mustafab0/Bionic-Arm/Design/Final/mini-dc-geared-motor-1.snapshot.2/mini dc geared motor02.JPG

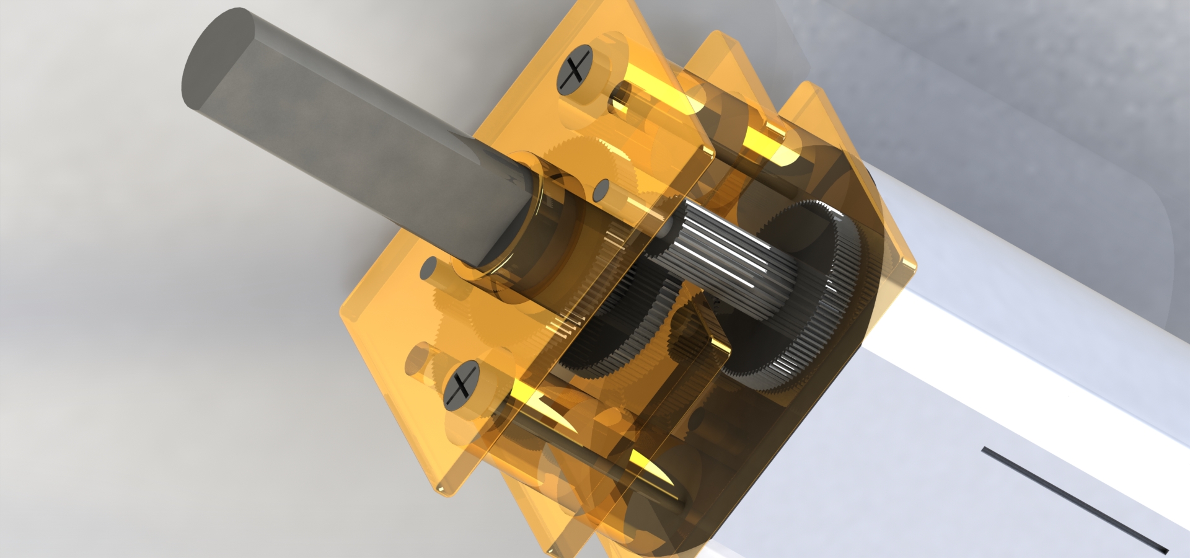
Design/Final/mini-dc-geared-motor-1.snapshot.2/mini dc geared motor02.JPG
