mustafab0/Bionic-Arm/Design/Final/mini-dc-geared-motor-1.snapshot.2/mini dc geared motor03.JPG

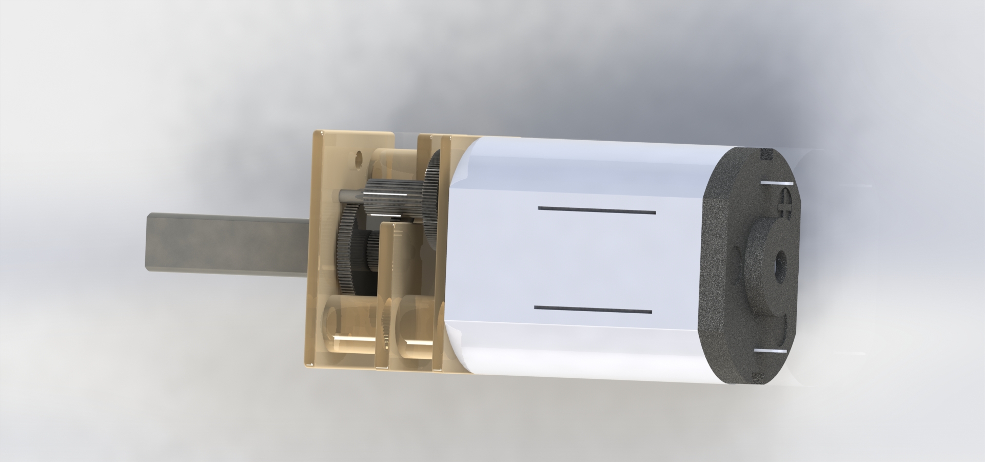
Design/Final/mini-dc-geared-motor-1.snapshot.2/mini dc geared motor03.JPG
