mustafab0/Bionic-Arm/Design/Final/mini-dc-geared-motor-1.snapshot.2/motorDC01.jpg

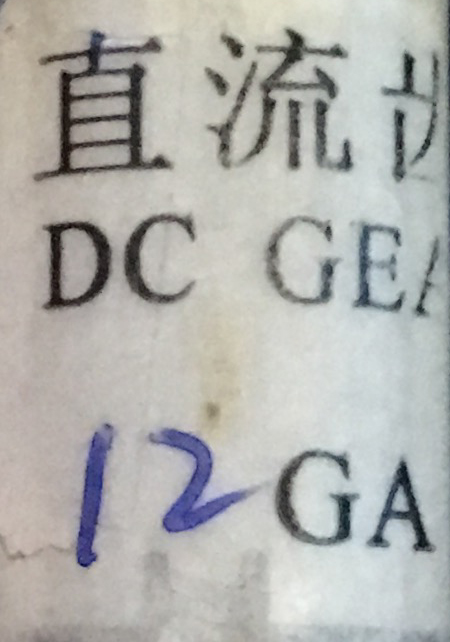
Design/Final/mini-dc-geared-motor-1.snapshot.2/motorDC01.jpg
