mustafab0/Bionic-Arm/Design/Final/mini-dc-geared-motor-1.snapshot.2/motorDC02.jpg

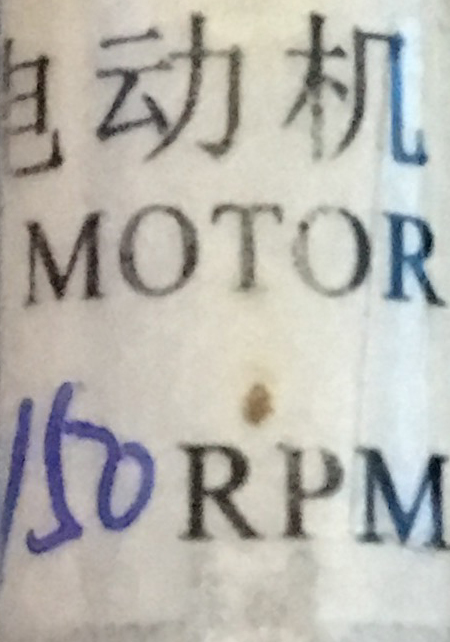
Design/Final/mini-dc-geared-motor-1.snapshot.2/motorDC02.jpg
