mustafab0/Bionic-Arm/Design/Hand/546.JPG

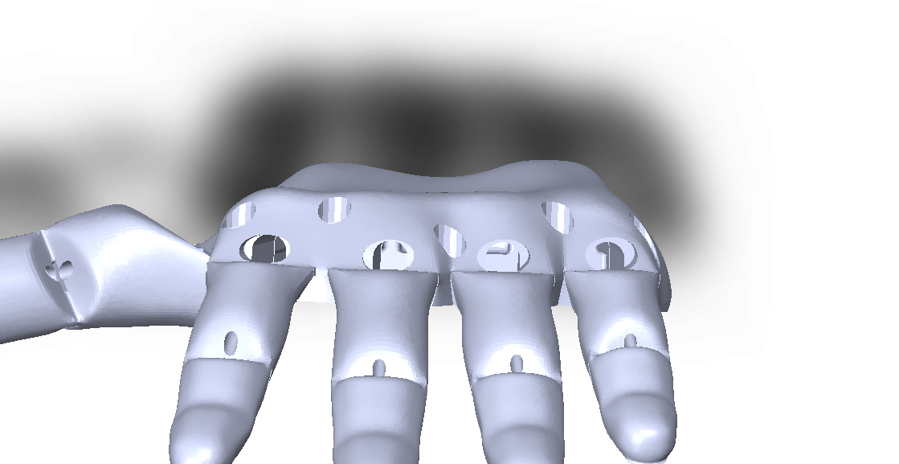
Design/Hand/546.JPG
