mustafab0/Bionic-Arm/Design/Hand/Arm.PNG

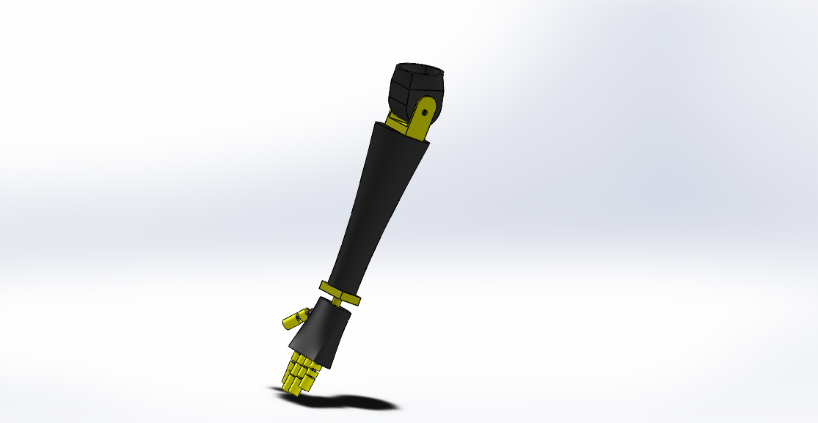
Design/Hand/Arm.PNG
