mustafab0/Bionic-Arm/Design/Images/Palm2.1.JPG

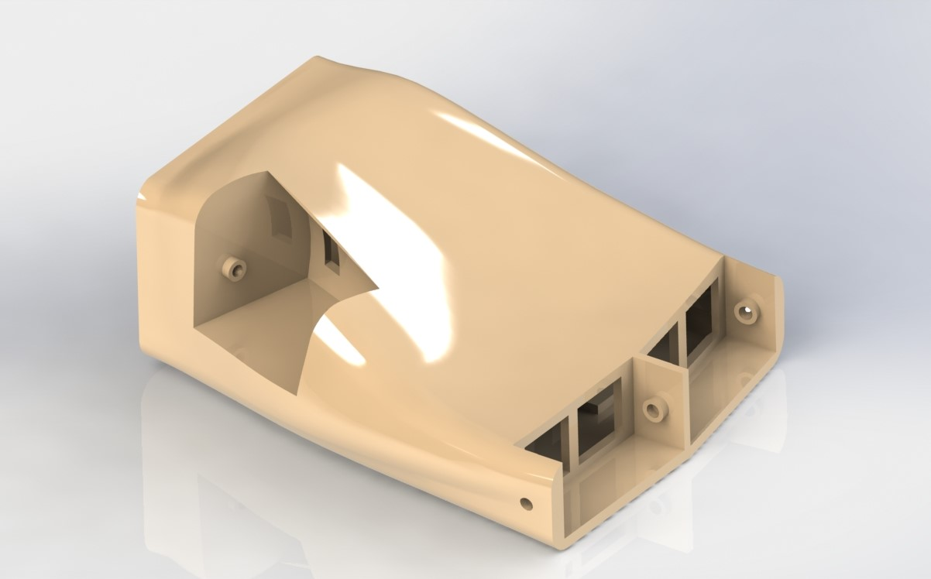
Design/Images/Palm2.1.JPG
