mustafab0/Bionic-Arm/Design/Palm/1.x/IMG_20170302_203847119.jpg

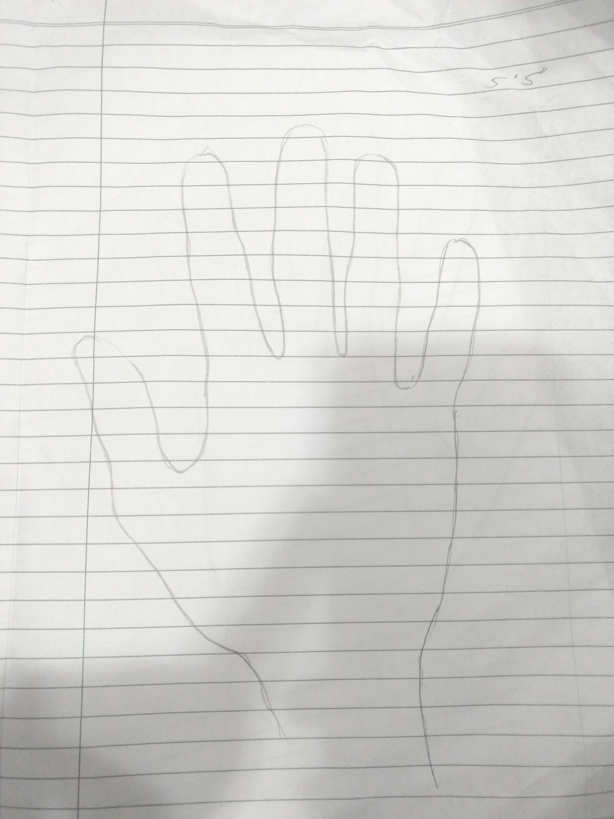
Design/Palm/1.x/IMG_20170302_203847119.jpg
