mustafab0/Bionic-Arm/Design/Fingers/2ndDigit/1.x/Index1.1.SLDASM

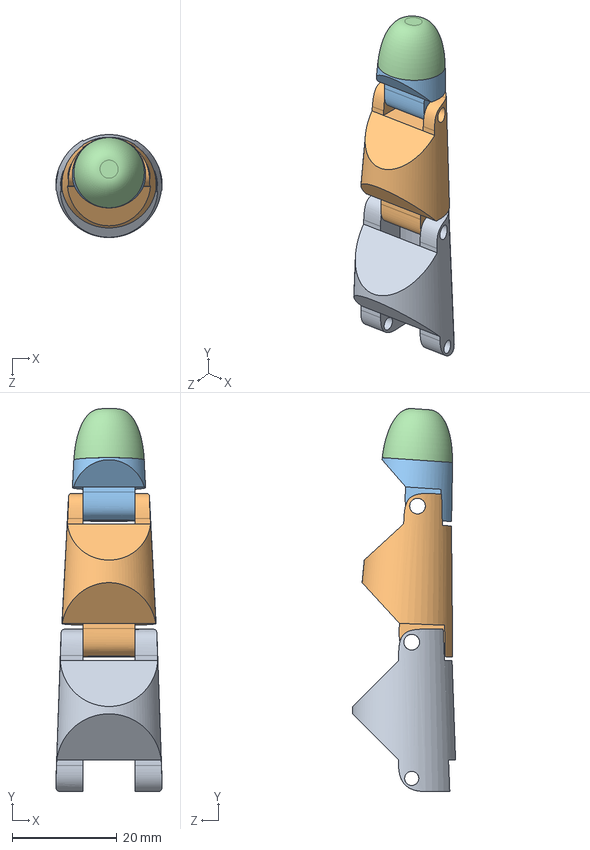
[picture p99: CAD file, 2022-01-19]
Design/Fingers/2ndDigit/1.x/Index1.1.SLDASM
20.3 x 73.1 x 19.7 mm
IBase1.1
IMid1.1
ITop1.1
ICap
