mustafab0/Bionic-Arm/Design/Fingers/3rdDigit/1.x/Middle1.1.1.SLDASM

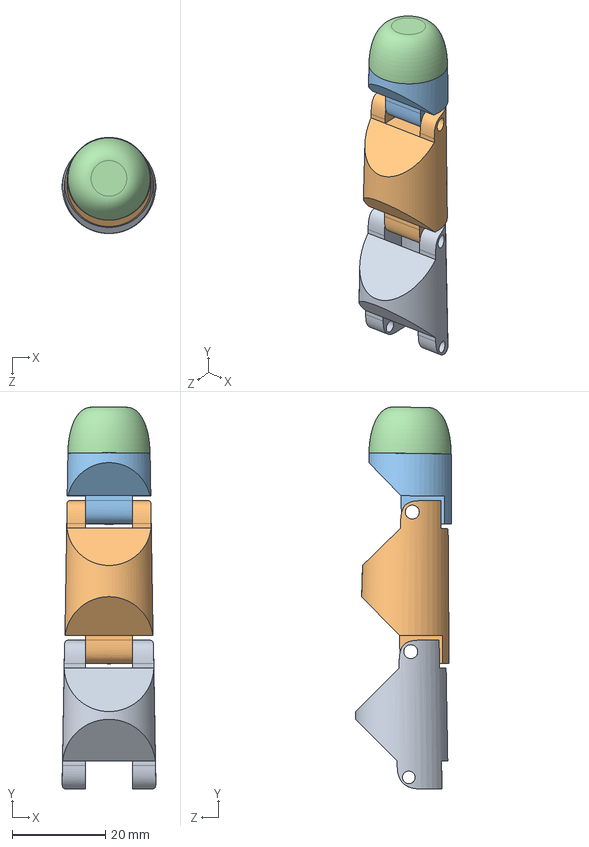
[picture p100: CAD file, 2022-01-19]
Design/Fingers/3rdDigit/1.x/Middle1.1.1.SLDASM
20.2 x 82.1 x 20.7 mm
MBase1.1
MMid1.1.1
MTop1.1.1
MCap1.1.1
