mustafab0/Bionic-Arm/Design/Hand/Assem2.0.1.SLDASM

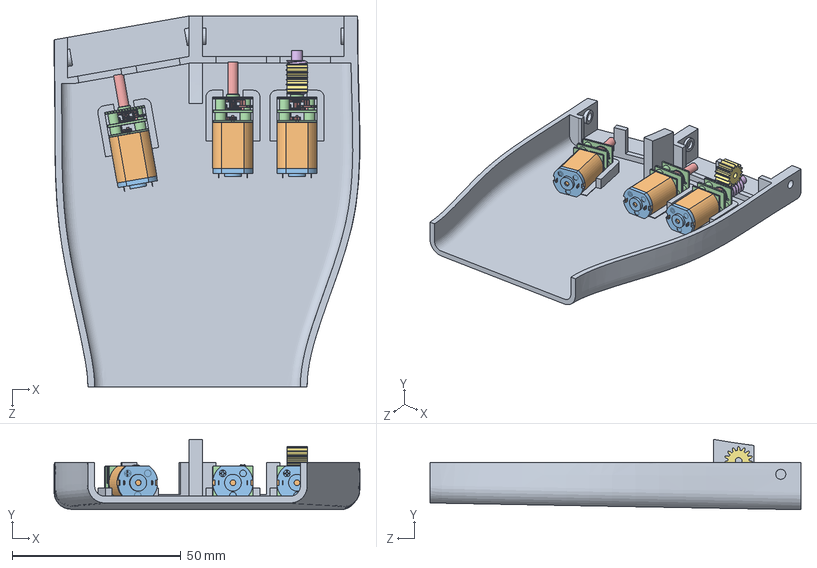
[picture p101: CAD file, 2022-01-19]
Design/Hand/Assem2.0.1.SLDASM
90.7 x 20.9 x 110.0 mm
Palm2.0.1
DC_GE_RED_Motor_01 x 3
DC_GE_RED_Motor_02 x 3
DC_GE_RED_Motor_03 x 3
DC_GE_RED_Motor_04 x 3
Worm Gear
spur gear_am
