mustafab0/Bionic-Arm/Design/Hand/BE Project/Assem3.1.1.SLDASM

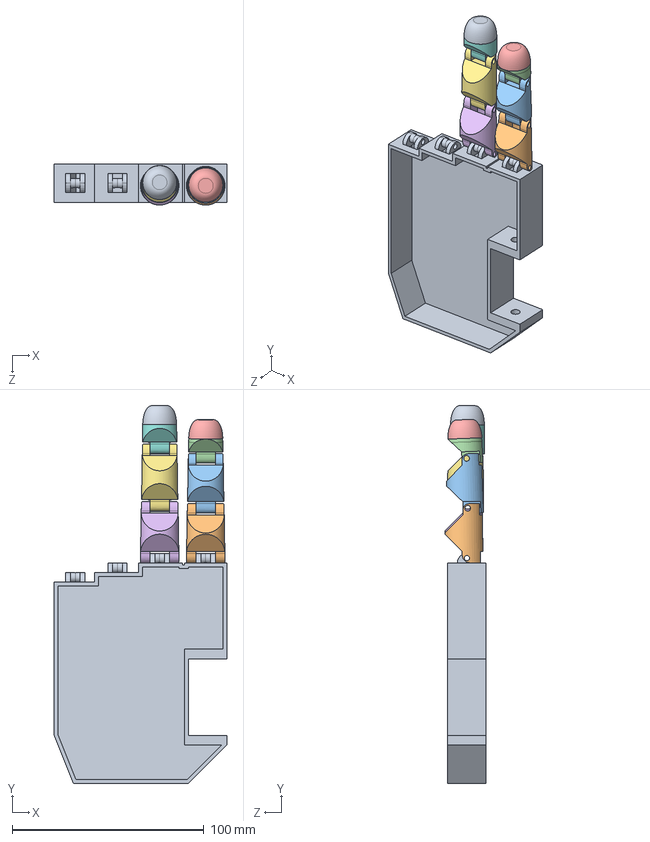
[picture p102: CAD file, 2022-01-19]
Design/Hand/BE Project/Assem3.1.1.SLDASM
90.0 x 197.1 x 21.5 mm
Palm1.0.1
IBase1.3
IMid1.3.1
ITop1.3.1
ICap1.3.1
MBase1.1
MMid1.1.1
MTop1.1.1
MCap1.1.1
