mustafab0/Bionic-Arm/Design/Fingers/1stDigit/1.x/Thumb1.0.SLDASM

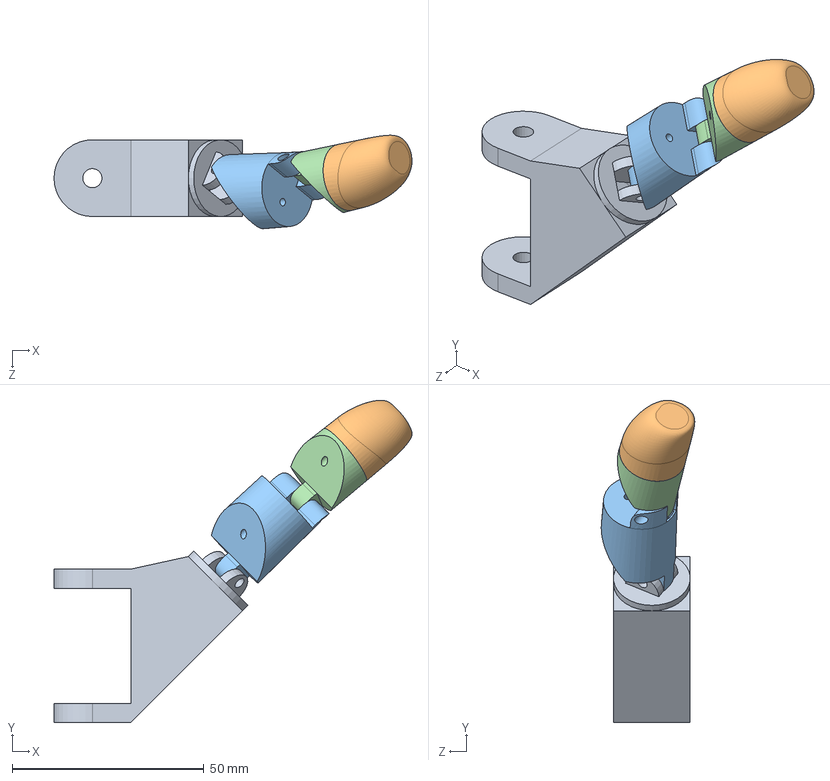
[picture p103: CAD file, 2022-01-19]
Design/Fingers/1stDigit/1.x/Thumb1.0.SLDASM
93.3 x 84.0 x 24.4 mm
TBase1.0
TCap1.0
TMid1.0
TTop1.0
