mustafab0/Bionic-Arm/Design/Fingers/3rdDigit/1.x/Middle1.0.SLDASM

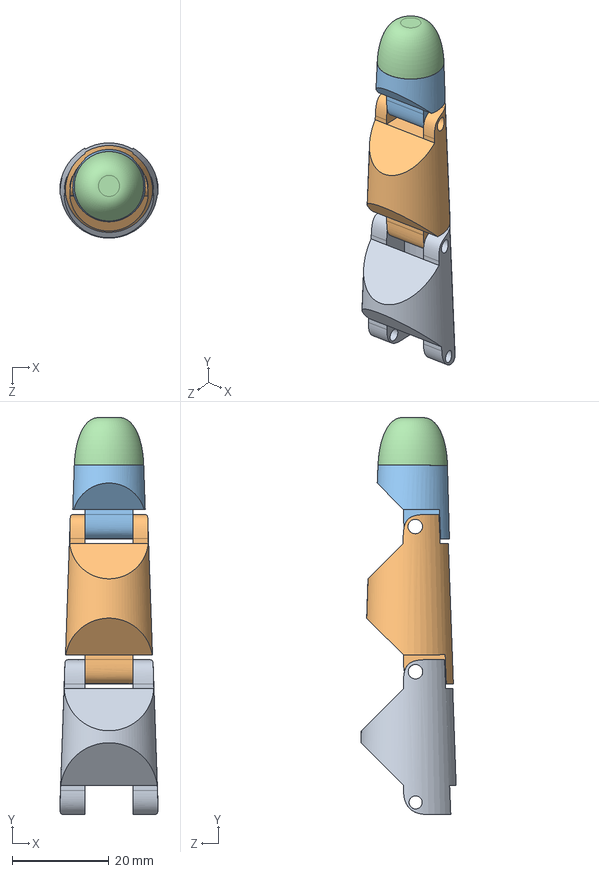
[picture p104: CAD file, 2022-01-19]
Design/Fingers/3rdDigit/1.x/Middle1.0.SLDASM
20.3 x 82.0 x 19.7 mm
MBase1.0
MMid1.0
MTop1.0
MCap1.0
