mustafab0/Bionic-Arm/Design/Palm/2.x/2.0.x/Assem2.SLDASM

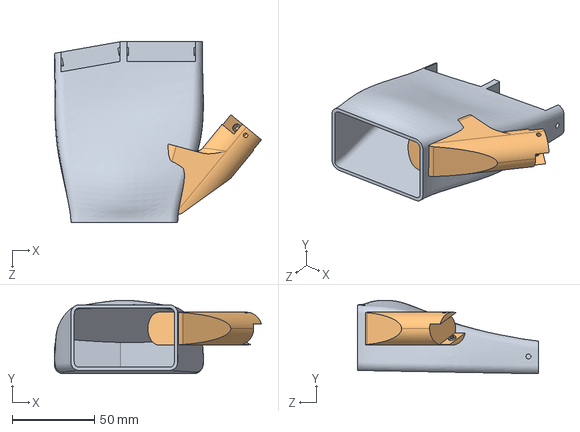
[picture p106: CAD file, 2022-01-19]
Design/Palm/2.x/2.0.x/Assem2.SLDASM
126.1 x 44.8 x 110.0 mm
Palm2.0
tProximal2.0
