mustafab0/Bionic-Arm/Design/Fingers/1stDigit/2.x/1Digit2.3.SLDASM

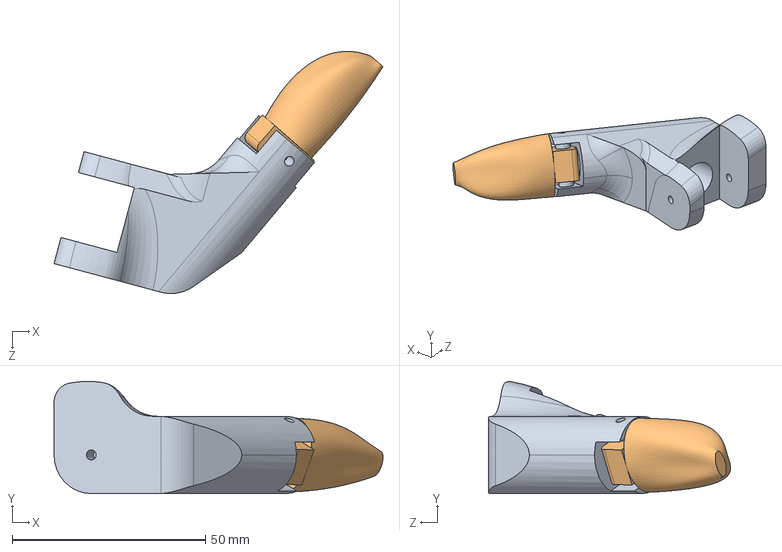
[picture p107: CAD file, 2022-01-19]
Design/Fingers/1stDigit/2.x/1Digit2.3.SLDASM
85.2 x 29.0 x 62.7 mm
tProximal2.3
tDistal2.0
