mustafab0/Bionic-Arm/Design/Hand/YadEKalKhair2.0Alternative mechanism.SLDASM

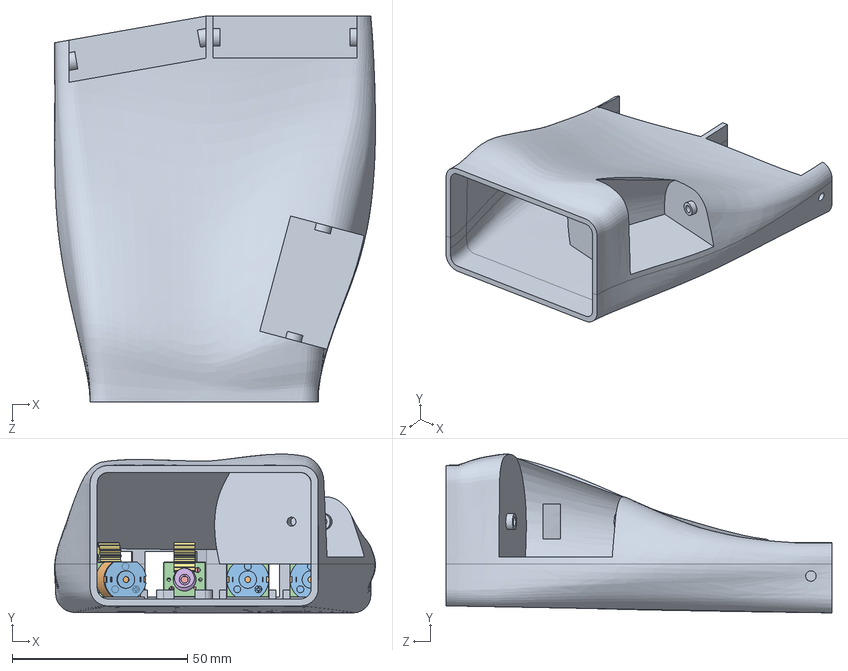
[picture p109: CAD file, 2022-01-19]
Design/Hand/YadEKalKhair2.0Alternative mechanism.SLDASM
91.5 x 45.3 x 110.0 mm
Palm2.2
DC_GE_RED_Motor_01 x 4
DC_GE_RED_Motor_02 x 4
DC_GE_RED_Motor_03 x 4
DC_GE_RED_Motor_04 x 4
Worm x 4
Spur Gear x 4
