mustafab0/Bionic-Arm/Design/Fingers/2ndDigit/1.x/Index1.2.SLDASM

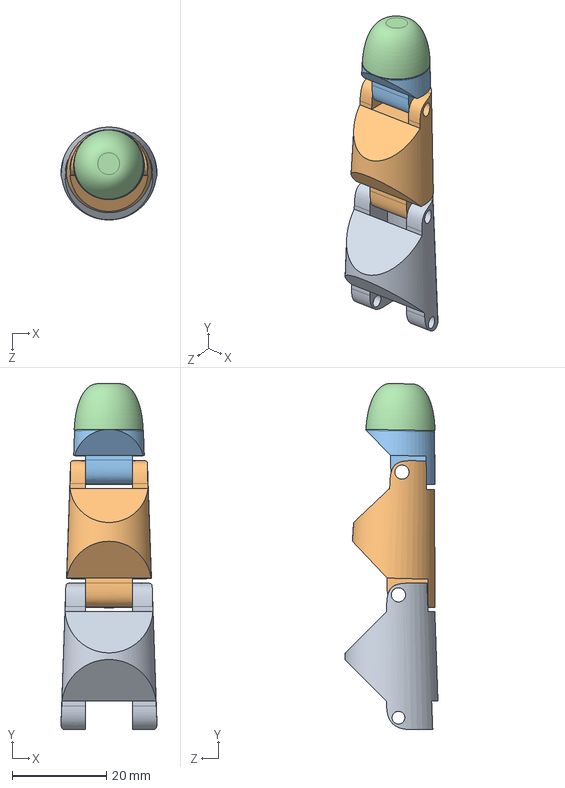
[picture p110: CAD file, 2022-01-19]
Design/Fingers/2ndDigit/1.x/Index1.2.SLDASM
20.3 x 73.3 x 19.7 mm
IBase1.1
IMid1.2
ITop1.2
ICap1.2
