mustafab0/Bionic-Arm/Design/Hand/BE Project/Assem1.SLDASM

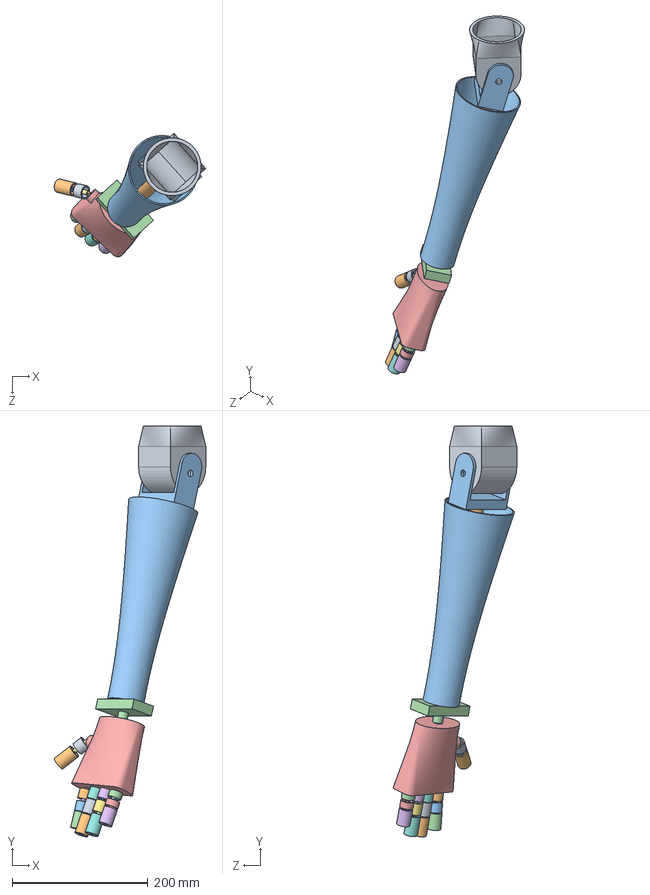
[picture p111: CAD file, 2022-01-19]
Design/Hand/BE Project/Assem1.SLDASM
223.2 x 605.1 x 182.0 mm
Stump1.0
ArmShaft1.0
Brace1.0
Brce
Palm1
IndexLFramework
IndexMFramework
IndexUFramework
Framework pin x 9
IndexL
IndexM
IndexU
MiddleLFramework
MiddleMFramework
MiddleUFramework
MiddleL
MiddleM
MiddleU
RingLFramework
RingMFramework
RingUFramework
RingL
RingM
RingU
PinkyLFramework
PinkyMFramework
PinkyUFramework
PinkyL
PinkyM
PinkyU
ThumbLFramework
ThumbUFramework
ThumbL
ThumbU
ArmCover
