mustafab0/Bionic-Arm/Design/Fingers/1stDigit/1.x/Thumb1.1.SLDASM

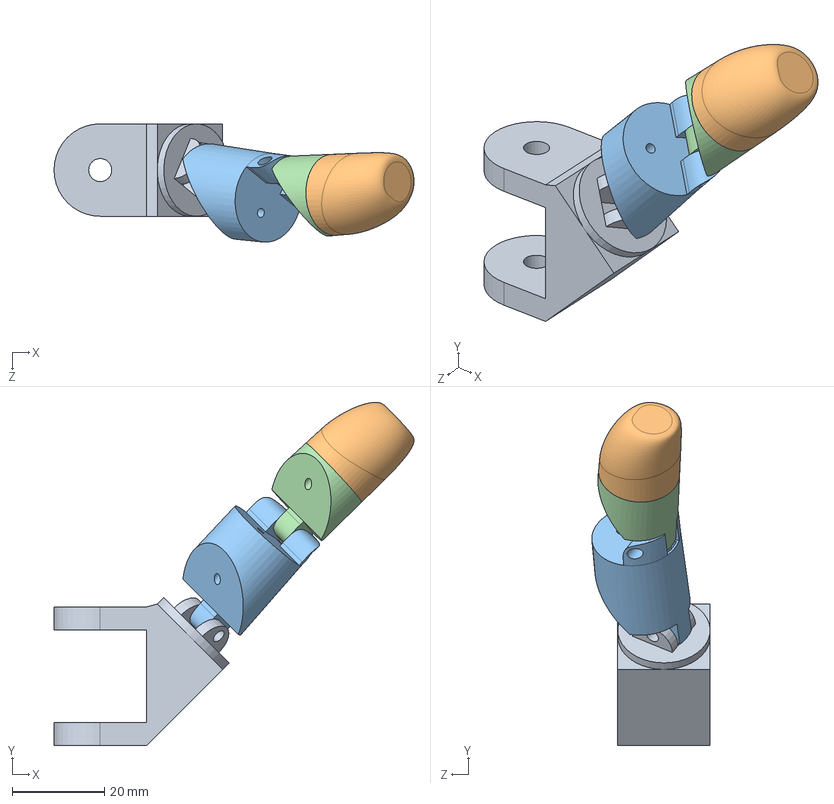
[picture p112: CAD file, 2022-01-19]
Design/Fingers/1stDigit/1.x/Thumb1.1.SLDASM
77.9 x 74.3 x 25.6 mm
TBase1.1
TCap1.0
TMid1.0
TTop1.0
