mustafab0/Bionic-Arm/Design/Fingers/1stDigit/2.x/1Digit2.2.SLDASM

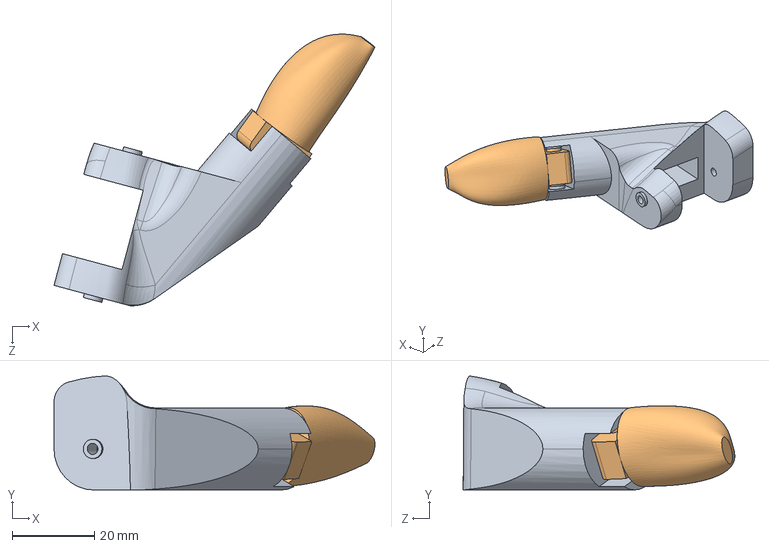
[picture p113: CAD file, 2022-01-19]
Design/Fingers/1stDigit/2.x/1Digit2.2.SLDASM
78.2 x 27.7 x 66.2 mm
tProximal2.2
tDistal2.0
