mustafab0/Bionic-Arm/Design/Fingers/3rdDigit/2.x/2.0/3Digit2.0.SLDASM

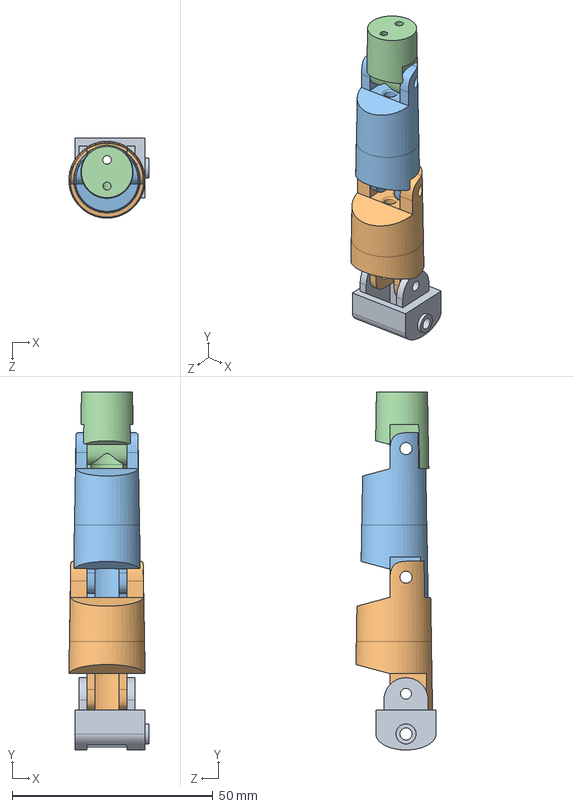
[picture p114: CAD file, 2022-01-19]
Design/Fingers/3rdDigit/2.x/2.0/3Digit2.0.SLDASM
20.0 x 89.1 x 20.0 mm
mMetaCarpal2.0
mProximal2.0
mIntermediate2.0
mDistal2.0
