mustafab0/Bionic-Arm/Design/Hand/BE Project/Assem.SLDASM

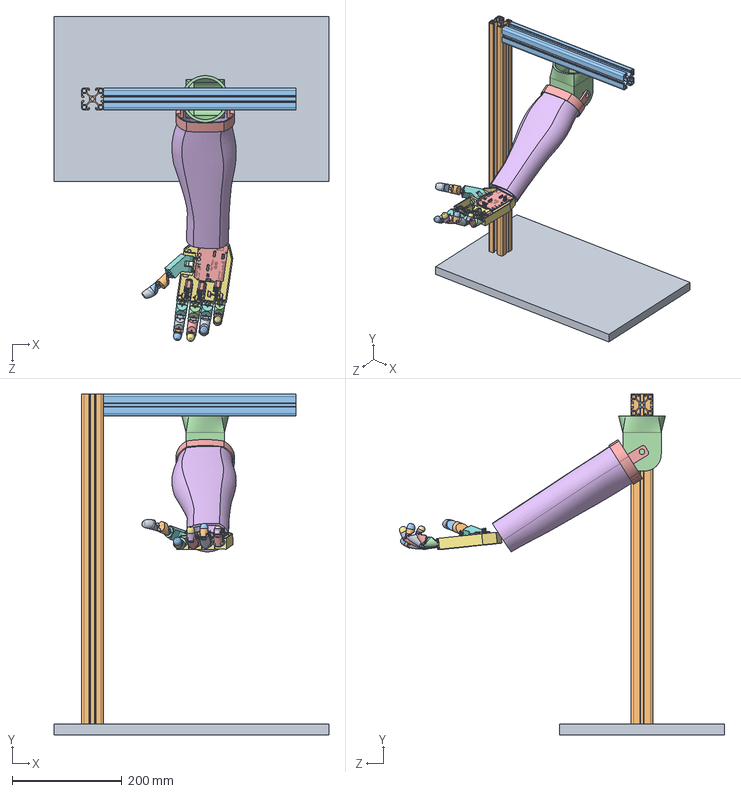
[picture p115: CAD file, 2022-01-19]
Design/Hand/BE Project/Assem.SLDASM
500.0 x 620.0 x 590.9 mm
Stump1.1
Brace1.1
ArmCover1.2
Palm1.0.4
IBase1.3
IMid1.3
ITop1.3
ICap1.3
Pulley Gear Shaft x 4
DC_GE_RED_Motor_01 x 4
DC_GE_RED_Motor_02 x 4
DC_GE_RED_Motor_03 x 4
DC_GE_RED_Motor_04 x 4
Worm Gear x 4
Pulley x 5
spur gear_am x 4
MBase1.1
MMid1.1
MTop1.1
MCap1.1
RBase1.0
RMid1.0
RTop1.0
RCap1.0
PBase1.0
PMid1.1
PTop1.1
PCap1.1
TBase1.2
TCap1.0
TMid1.0
TTop1.0
Pin
Arduino board
