mustafab0/Bionic-Arm/Design/Fingers/4thDigit/2.x/2.0/4Digit2.0.SLDASM

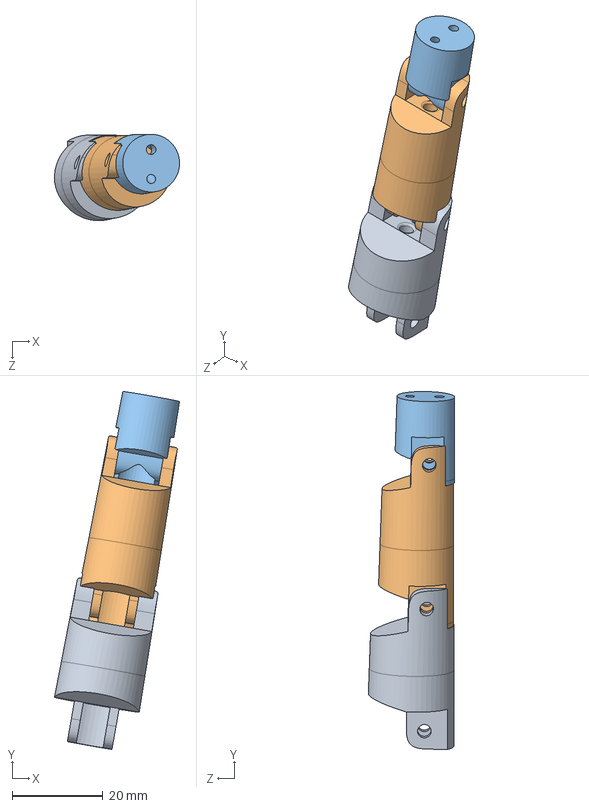
[picture p116: CAD file, 2022-01-19]
Design/Fingers/4thDigit/2.x/2.0/4Digit2.0.SLDASM
27.6 x 79.0 x 19.0 mm
rProximal2.0
rIntermediate2.0
rDistal2.0
