mustafab0/Bionic-Arm/Design/Fingers/5thDigit/1.x/Pinky1.0.SLDASM

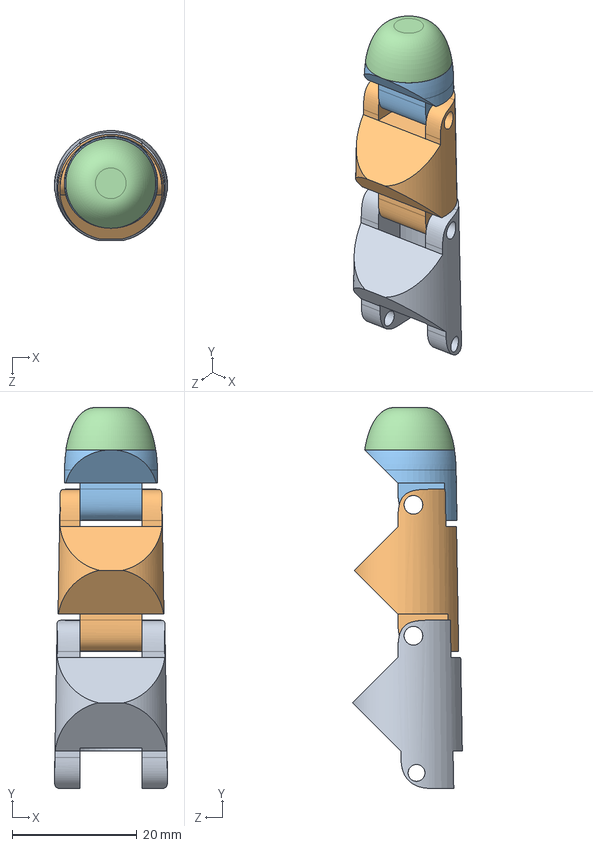
[picture p117: CAD file, 2022-01-19]
Design/Fingers/5thDigit/1.x/Pinky1.0.SLDASM
18.2 x 61.1 x 17.6 mm
PBase1.0
PMid1.0
PTop1.0
PCap1.0
