mustafab0/Bionic-Arm/Design/Fingers/5thDigit/2.x/5Digit2.0.SLDASM

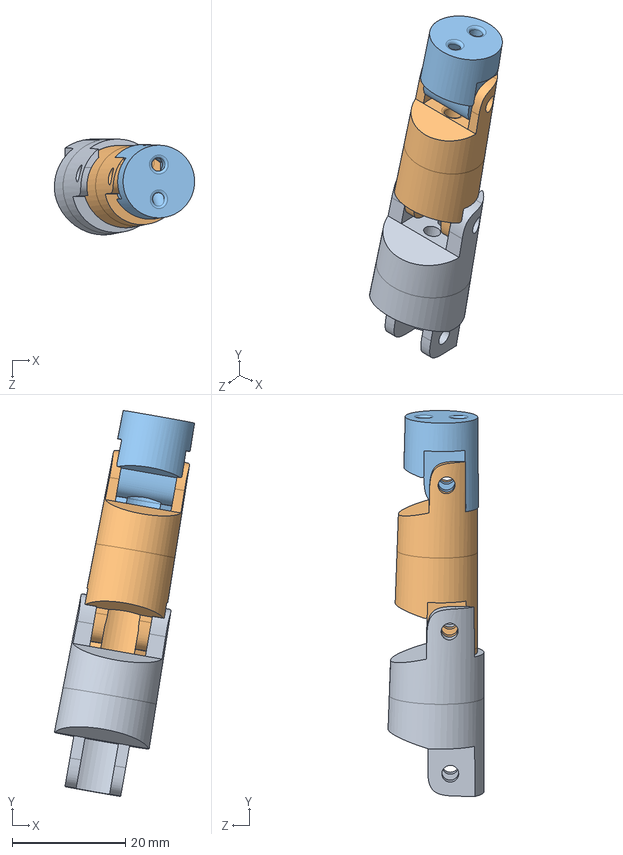
[picture p118: CAD file, 2022-01-19]
Design/Fingers/5thDigit/2.x/5Digit2.0.SLDASM
24.8 x 68.2 x 16.9 mm
pProximal2.0
pIntermediate2.0
pDistal2.0
