mustafab0/Bionic-Arm/Design/Fingers/1stDigit/1.x/Thumb1.2.SLDASM

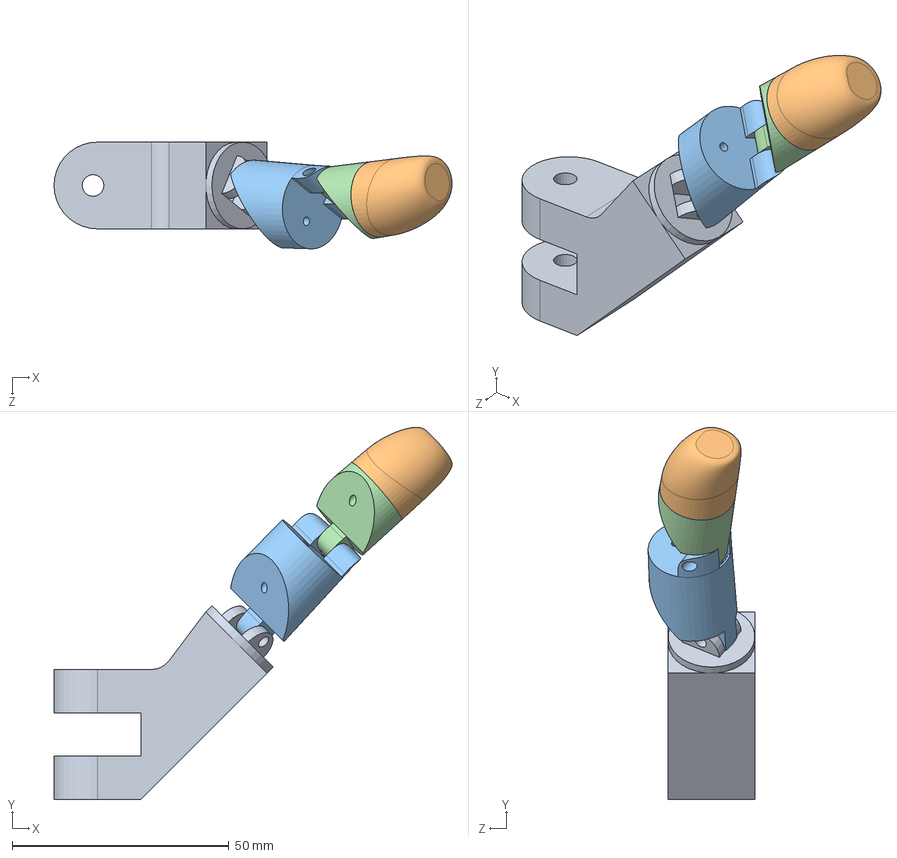
[picture p119: CAD file, 2022-01-19]
Design/Fingers/1stDigit/1.x/Thumb1.2.SLDASM
91.8 x 85.8 x 24.6 mm
TBase1.2
TCap1.0
TMid1.0
TTop1.0
