mustafab0/Bionic-Arm/Design/Hand/BE Project/Assem4.SLDASM

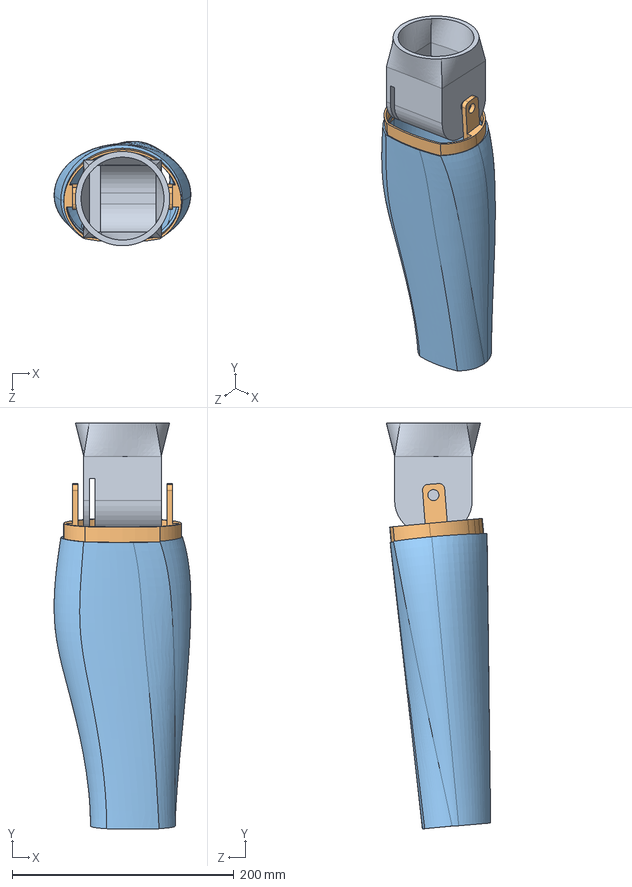
[picture p120: CAD file, 2022-01-19]
Design/Hand/BE Project/Assem4.SLDASM
123.3 x 366.0 x 94.2 mm
Stump1.1
Brace1.1
ArmCover1.1
