mustafab0/Bionic-Arm/Design/Hand/BE Project/Assem5.SLDASM

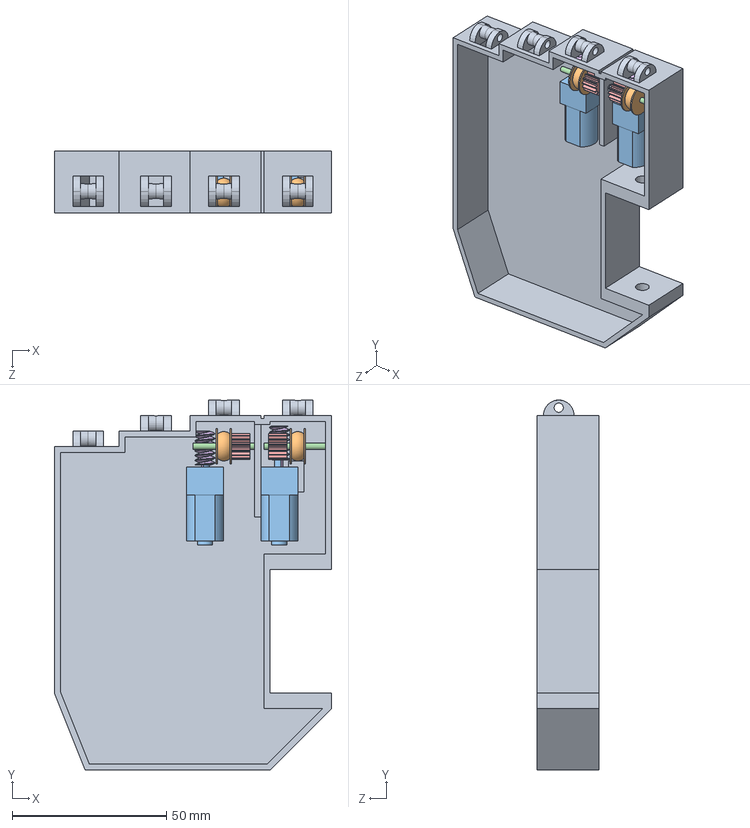
[picture p121: CAD file, 2022-01-19]
Design/Hand/BE Project/Assem5.SLDASM
90.0 x 120.0 x 20.0 mm
Palm1.0.2
Small Pulley x 2
Mini DC Motor x 2
Pulley Gear Shaft x 2
spur gear_am x 2
Worm Gear x 2
