mustafab0/Bionic-Arm/Design/Final/Assem1.SLDASM

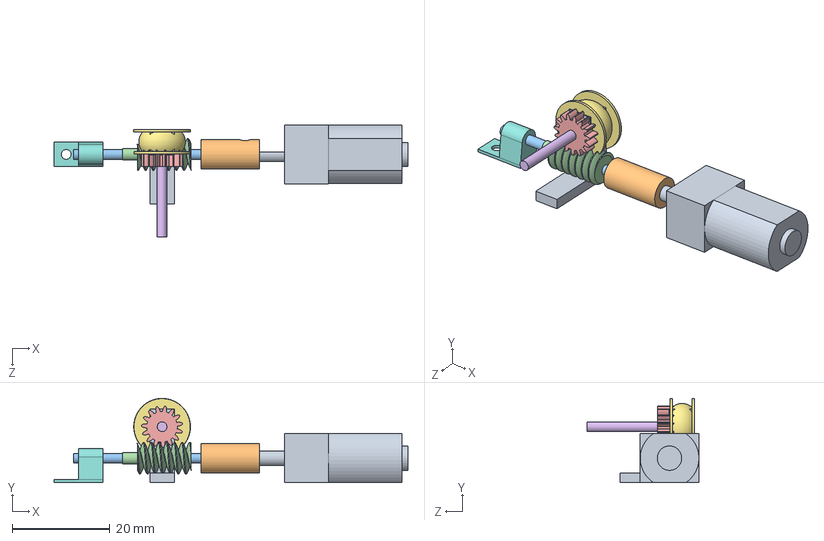
[picture p122: CAD file, 2022-01-19]
Design/Final/Assem1.SLDASM
72.3 x 17.2 x 22.9 mm
Mini DC Motor
Coupling
Shaft for coupling n
Worm Gear
spur gear_am
Pulley Gear Shaft
Small Pulley
Support
Support1
