mustafab0/Bionic-Arm/Design/Fingers/3rdDigit/1.x/Middle1.1.SLDASM

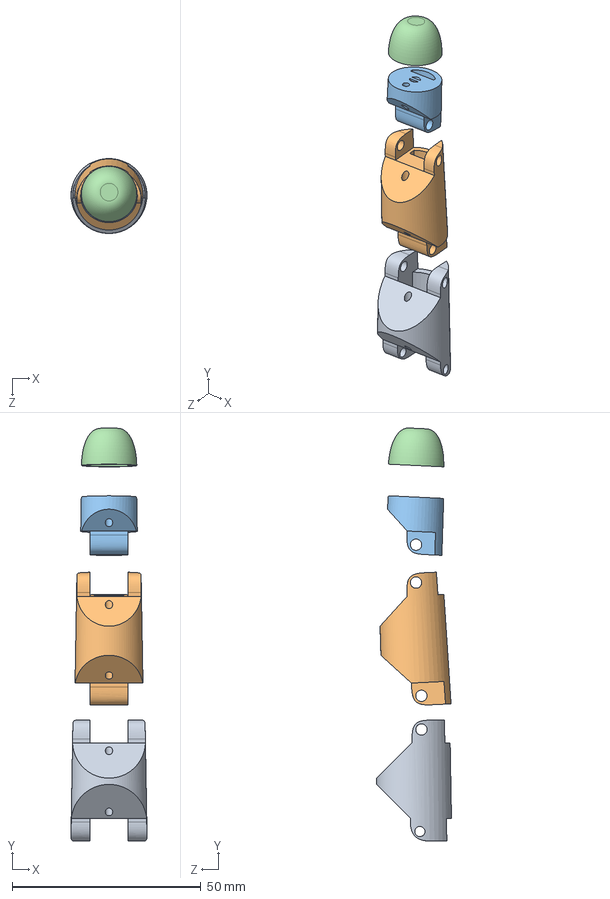
[picture p123: CAD file, 2022-01-19]
Design/Fingers/3rdDigit/1.x/Middle1.1.SLDASM
20.2 x 109.3 x 19.8 mm
MBase1.1
MMid1.1
MTop1.1
MCap1.1
