mustafab0/Bionic-Arm/Design/Hand/BE Project/Assem3.1.2.SLDASM

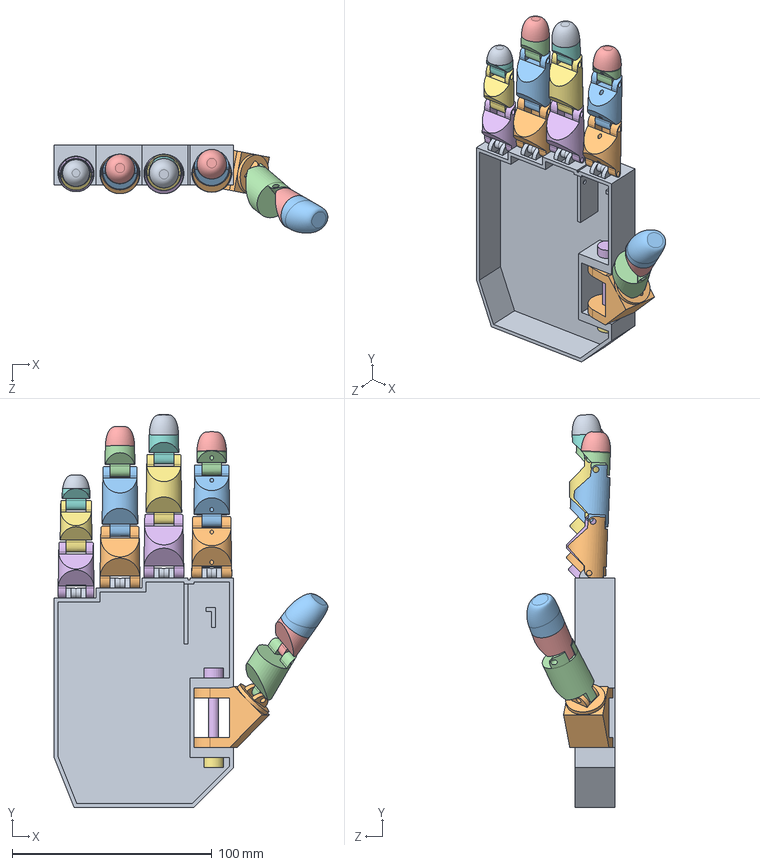
[picture p124: CAD file, 2022-01-19]
Design/Hand/BE Project/Assem3.1.2.SLDASM
137.2 x 197.0 x 44.2 mm
Palm1.0.4
IBase1.3
IMid1.3
ITop1.3
ICap1.3
MBase1.1
MMid1.1
MTop1.1
MCap1.1
RBase1.0
RMid1.0
RTop1.0
RCap1.0
PBase1.0
PMid1.1
PTop1.1
PCap1.1
TBase1.1
TCap1.0
TMid1.0
TTop1.0
Part3^Assem3.1.2
Part4^Assem3.1.2
