mustafab0/Bionic-Arm/Design/Fingers/2ndDigit/1.x/Index1.3.SLDASM

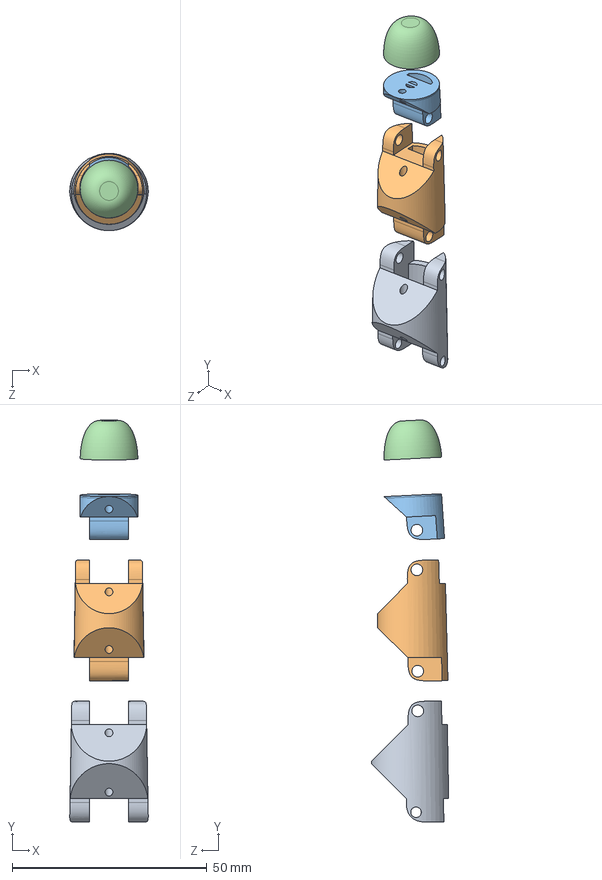
[picture p125: CAD file, 2022-01-19]
Design/Fingers/2ndDigit/1.x/Index1.3.SLDASM
20.2 x 103.1 x 19.8 mm
IBase1.3
IMid1.3
ITop1.3
ICap1.3
