mustafab0/Bionic-Arm/Design/Final/Arduino board.SLDPRT

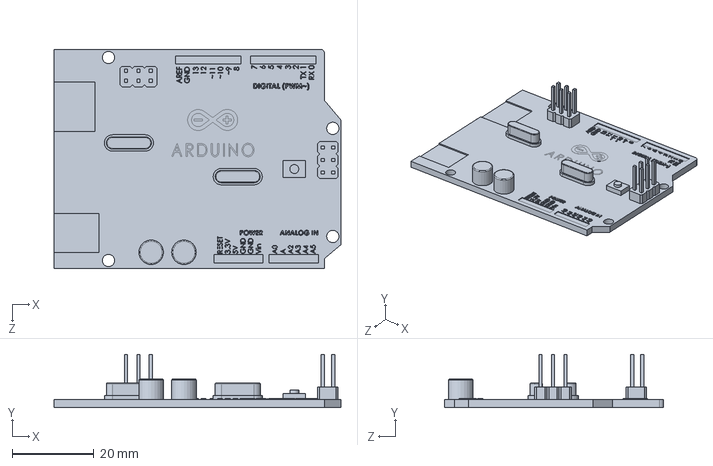
[picture p126: CAD file, 2022-01-19]
Design/Final/Arduino board.SLDPRT
70.0 x 13.0 x 53.5 mm
