mustafab0/Bionic-Arm/Design/Final/mini-dc-geared-motor-1.snapshot.2/DC_GE_RED_Motor_03.SLDPRT

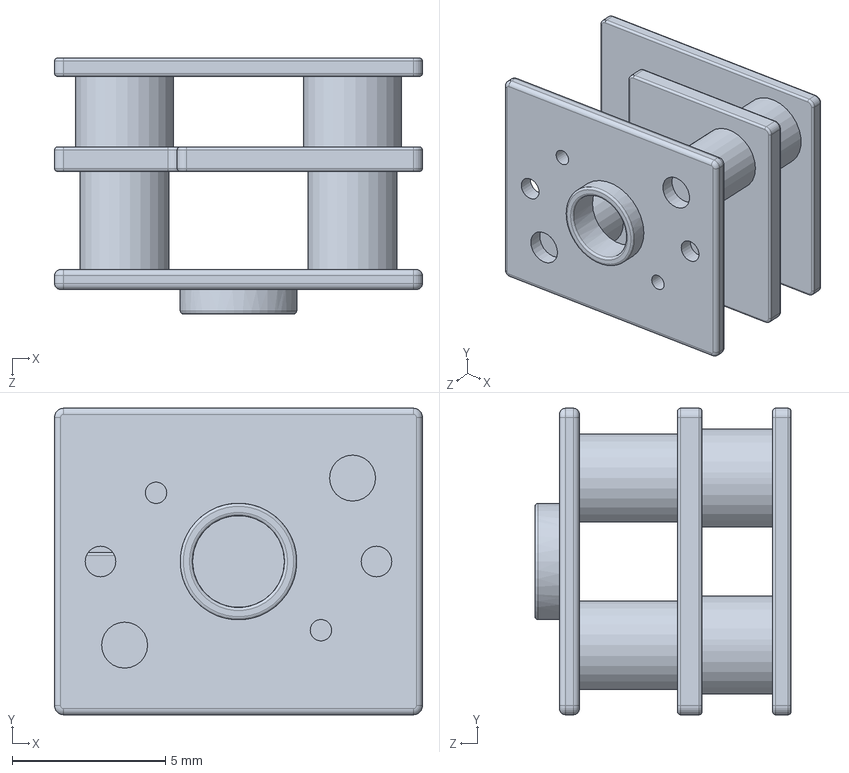
[picture p127: CAD file, 2022-01-19]
Design/Final/mini-dc-geared-motor-1.snapshot.2/DC_GE_RED_Motor_03.SLDPRT
12.0 x 10.0 x 8.35 mm
