mustafab0/Bionic-Arm/Design/Fingers/1stDigit/1.x/TCap1.0.SLDPRT

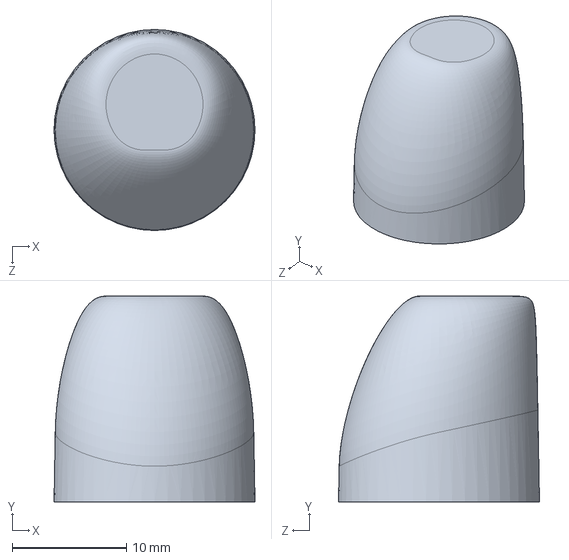
[picture p128: CAD file, 2022-01-19]
Design/Fingers/1stDigit/1.x/TCap1.0.SLDPRT
17.6 x 18.0 x 17.6 mm
