mustafab0/Bionic-Arm/Design/Fingers/1stDigit/2.x/tProximal2.3.SLDPRT

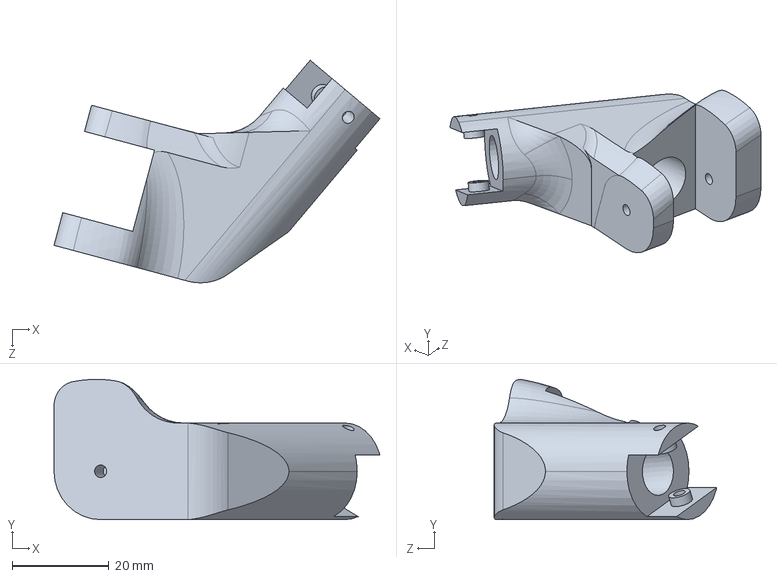
[picture p129: CAD file, 2022-01-19]
Design/Fingers/1stDigit/2.x/tProximal2.3.SLDPRT
67.5 x 29.0 x 46.1 mm
