mustafab0/Bionic-Arm/Design/Fingers/2ndDigit/1.x/ITop1.1.SLDPRT

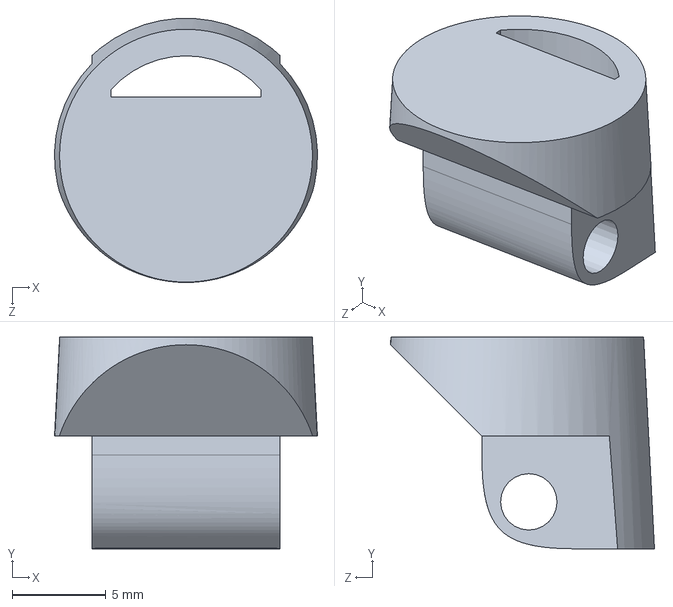
[picture p130: CAD file, 2022-01-19]
Design/Fingers/2ndDigit/1.x/ITop1.1.SLDPRT
14.0 x 11.3 x 14.0 mm
