mustafab0/Bionic-Arm/Design/Fingers/2ndDigit/2.x/2.0/LowerMid2.0.sldprt

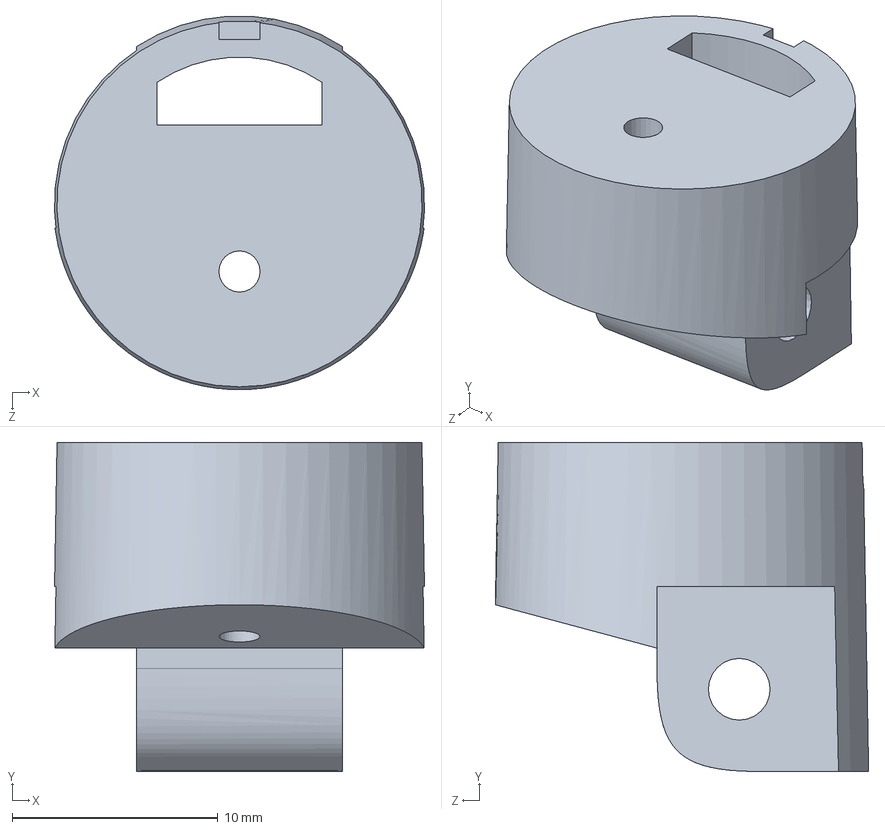
[picture p131: CAD file, 2022-01-19]
Design/Fingers/2ndDigit/2.x/2.0/LowerMid2.0.sldprt
18.0 x 16.0 x 18.2 mm
