mustafab0/Bionic-Arm/Design/Fingers/2ndDigit/2.x/2.1/iIntermediate2.1.SLDPRT

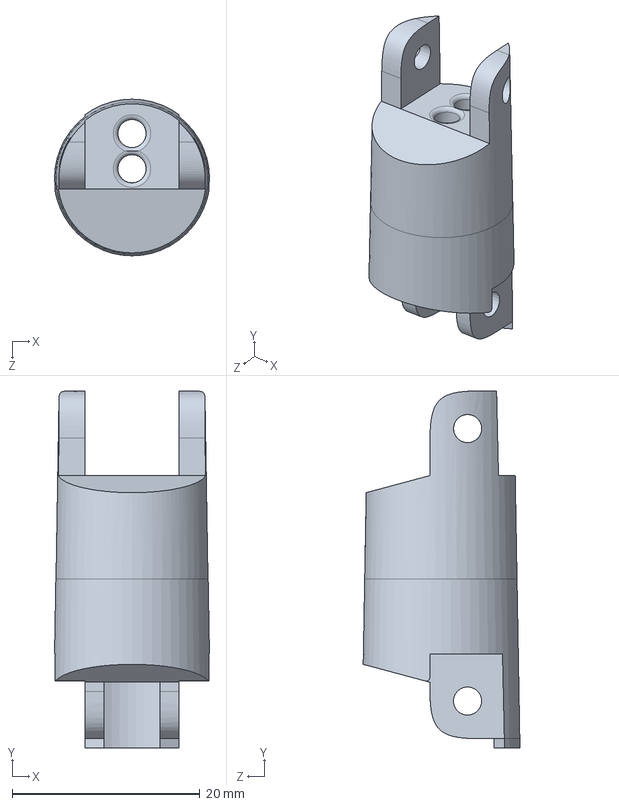
[picture p132: CAD file, 2022-01-19]
Design/Fingers/2ndDigit/2.x/2.1/iIntermediate2.1.SLDPRT
16.5 x 38.0 x 16.7 mm
