mustafab0/Bionic-Arm/Design/Fingers/3rdDigit/1.x/MCap1.0.SLDPRT

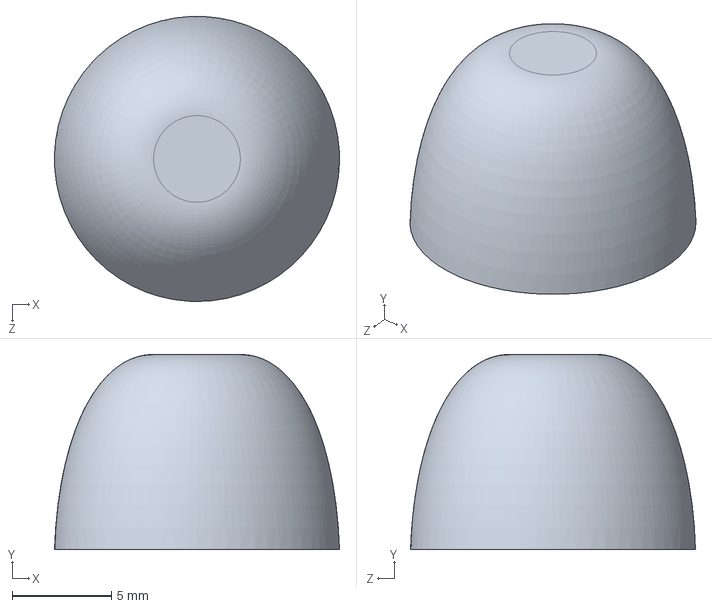
[picture p133: CAD file, 2022-01-19]
Design/Fingers/3rdDigit/1.x/MCap1.0.SLDPRT
14.4 x 9.83 x 14.4 mm
