mustafab0/Bionic-Arm/Design/Fingers/3rdDigit/2.x/2.0/mProximal2.0a.SLDPRT

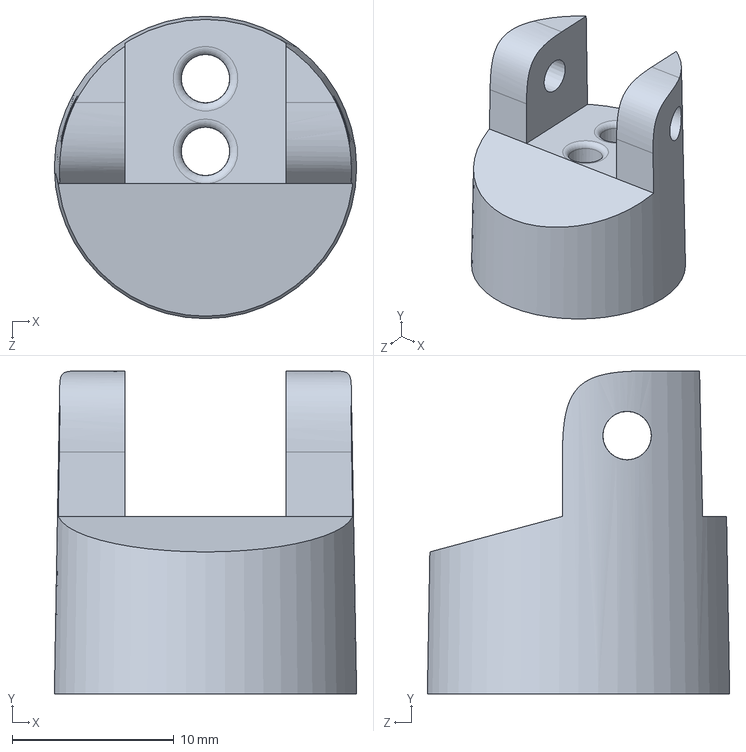
[picture p134: CAD file, 2022-01-19]
Design/Fingers/3rdDigit/2.x/2.0/mProximal2.0a.SLDPRT
18.7 x 20.0 x 18.7 mm
