mustafab0/Bionic-Arm/Design/Fingers/4thDigit/2.x/2.0/rIntermediate2.0a.SLDPRT

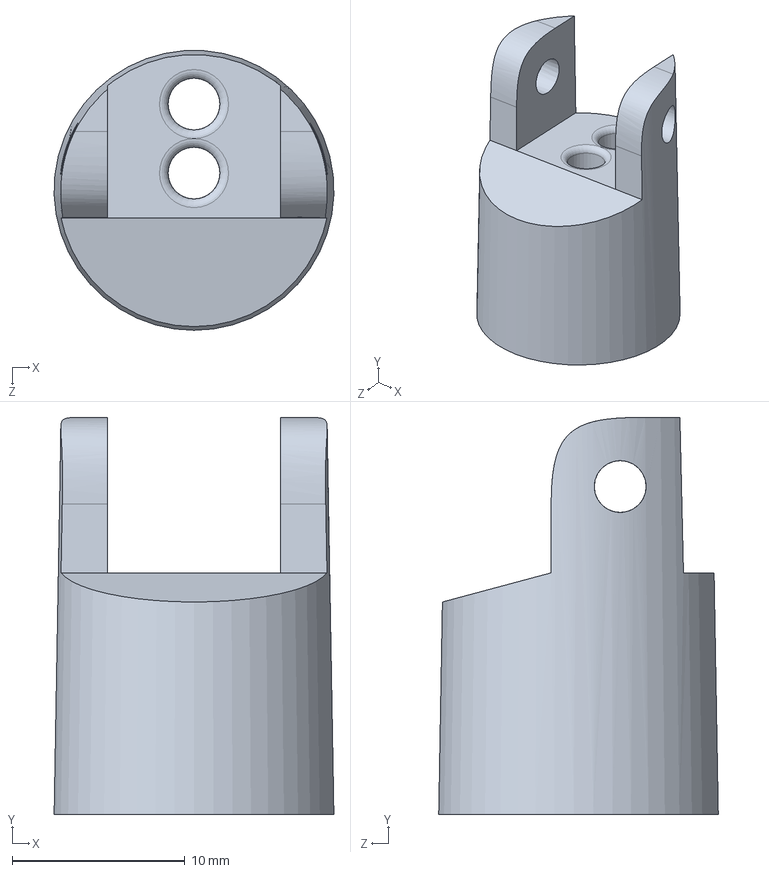
[picture p135: CAD file, 2022-01-19]
Design/Fingers/4thDigit/2.x/2.0/rIntermediate2.0a.SLDPRT
16.2 x 23.0 x 16.2 mm
