mustafab0/Bionic-Arm/Design/Fingers/4thDigit/2.x/2.1/rMetaCarpal2.1.SLDPRT

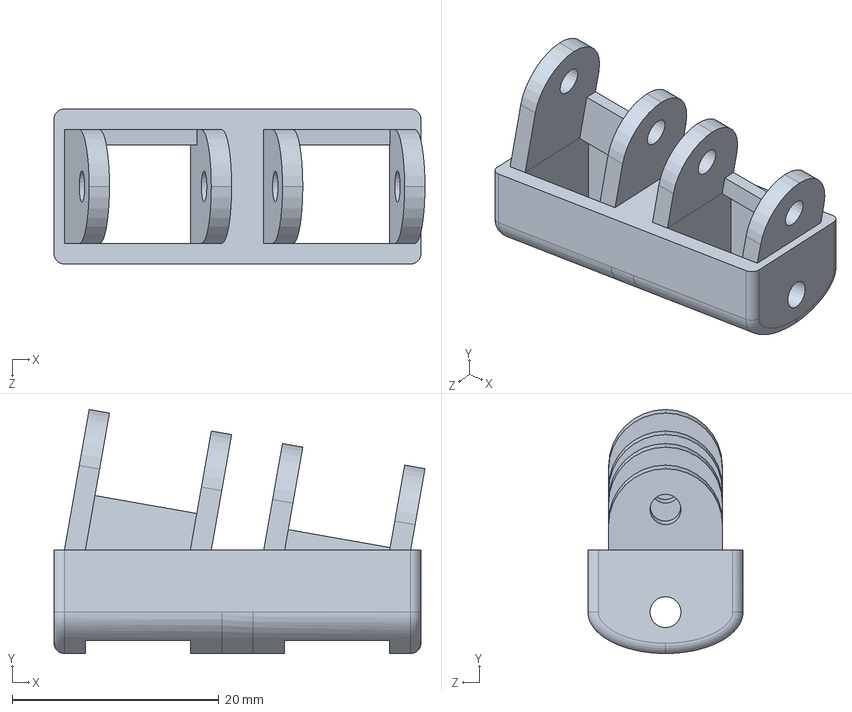
[picture p136: CAD file, 2022-01-19]
Design/Fingers/4thDigit/2.x/2.1/rMetaCarpal2.1.SLDPRT
35.9 x 23.6 x 15.0 mm
