mustafab0/Bionic-Arm/Design/Hand/BE Project/Palm.SLDPRT

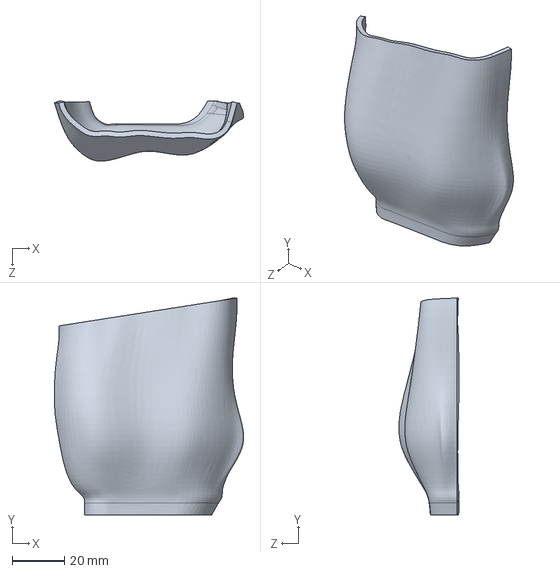
[picture p138: CAD file, 2022-01-19]
Design/Hand/BE Project/Palm.SLDPRT
72.1 x 82.7 x 23.0 mm
