mustafab0/Bionic-Arm/Design/Palm/1.x/Base1.SLDPRT

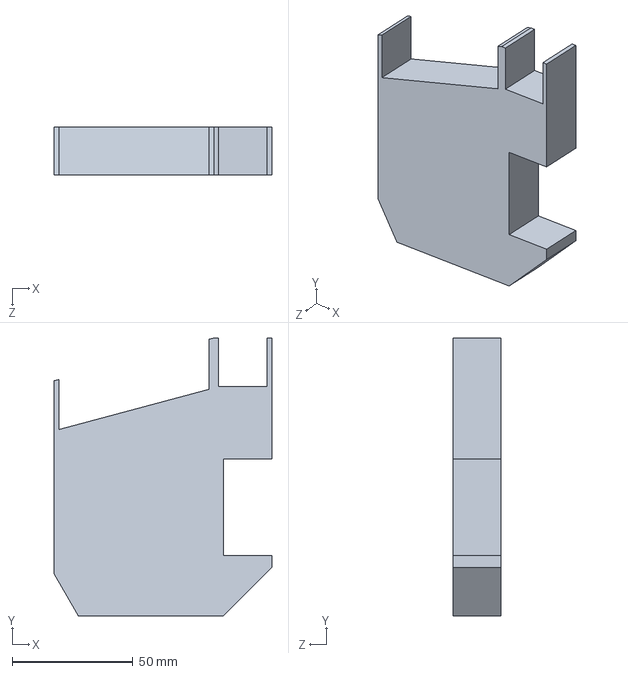
[picture p139: CAD file, 2022-01-19]
Design/Palm/1.x/Base1.SLDPRT
90.0 x 115.0 x 20.0 mm
