mustafab0/Bionic-Arm/Design/Palm/2.x/2.1.x/Palm2.2.SLDPRT

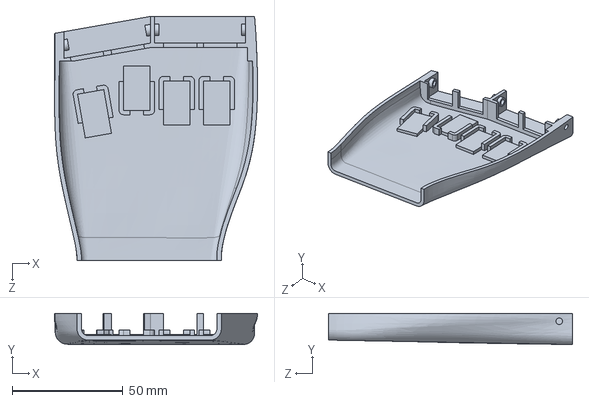
[picture p141: CAD file, 2022-01-19]
Design/Palm/2.x/2.1.x/Palm2.2.SLDPRT
91.5 x 14.0 x 110.0 mm
