mustafab0/Bionic-Arm/Design/Final/Big Pulley.SLDPRT

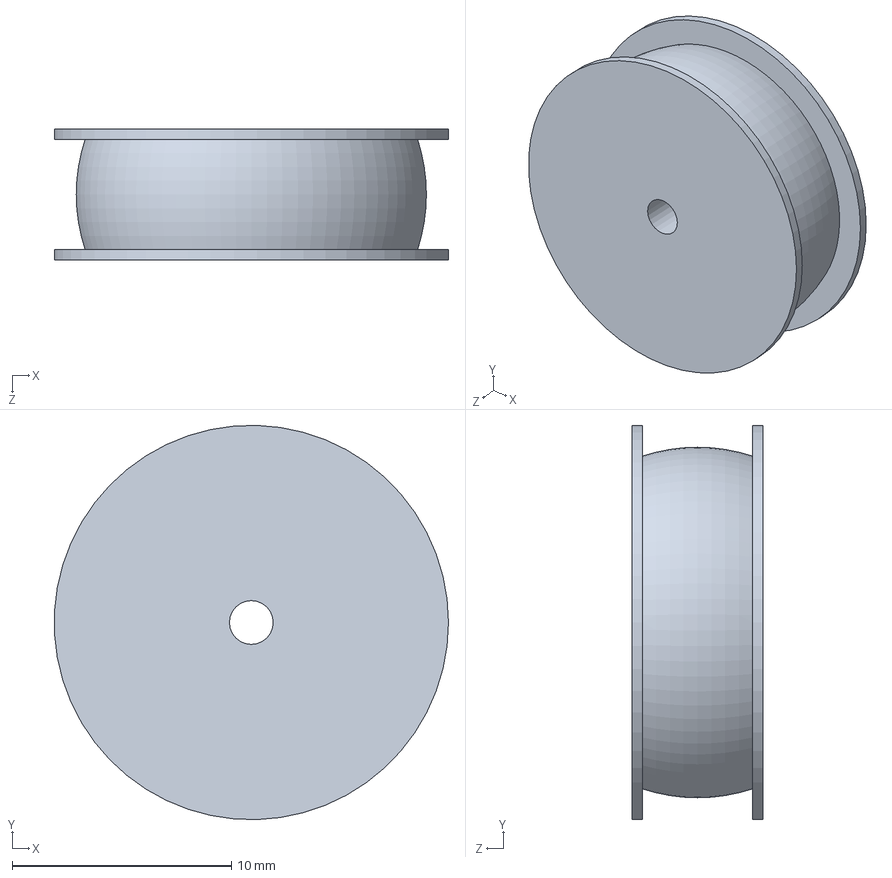
[picture p142: CAD file, 2022-01-19]
Design/Final/Big Pulley.SLDPRT
18.0 x 18.0 x 6.00 mm
