mustafab0/Bionic-Arm/Design/Final/mini-dc-geared-motor-1.snapshot.2/DC_GE_RED_Motor_01.SLDPRT

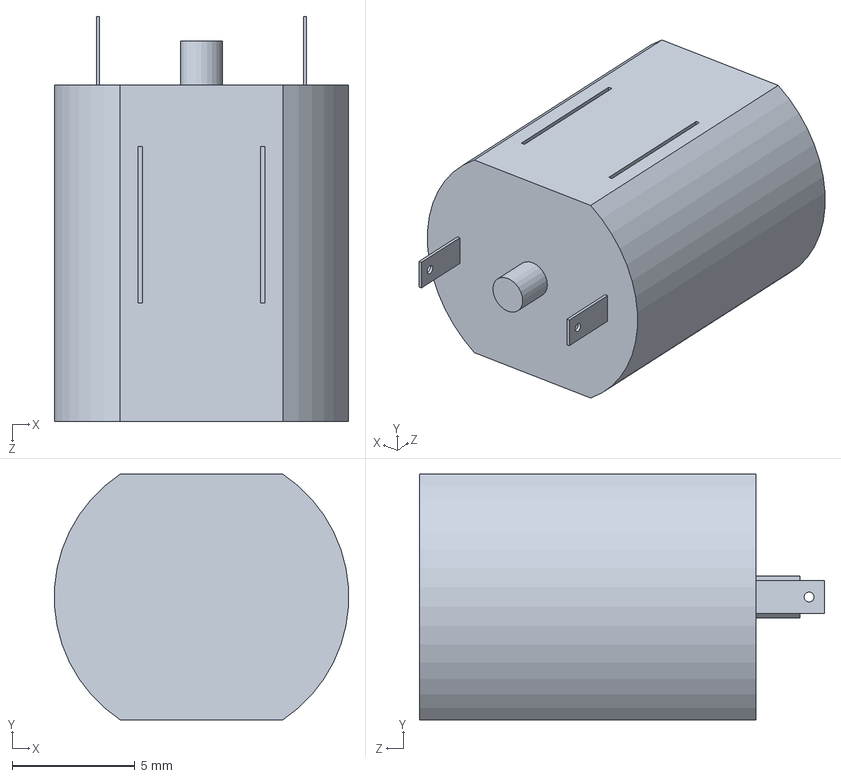
[picture p143: CAD file, 2022-01-19]
Design/Final/mini-dc-geared-motor-1.snapshot.2/DC_GE_RED_Motor_01.SLDPRT
12.0 x 10.0 x 16.5 mm
