mustafab0/Bionic-Arm/Design/Fingers/1stDigit/1.x/TBase1.2.SLDPRT

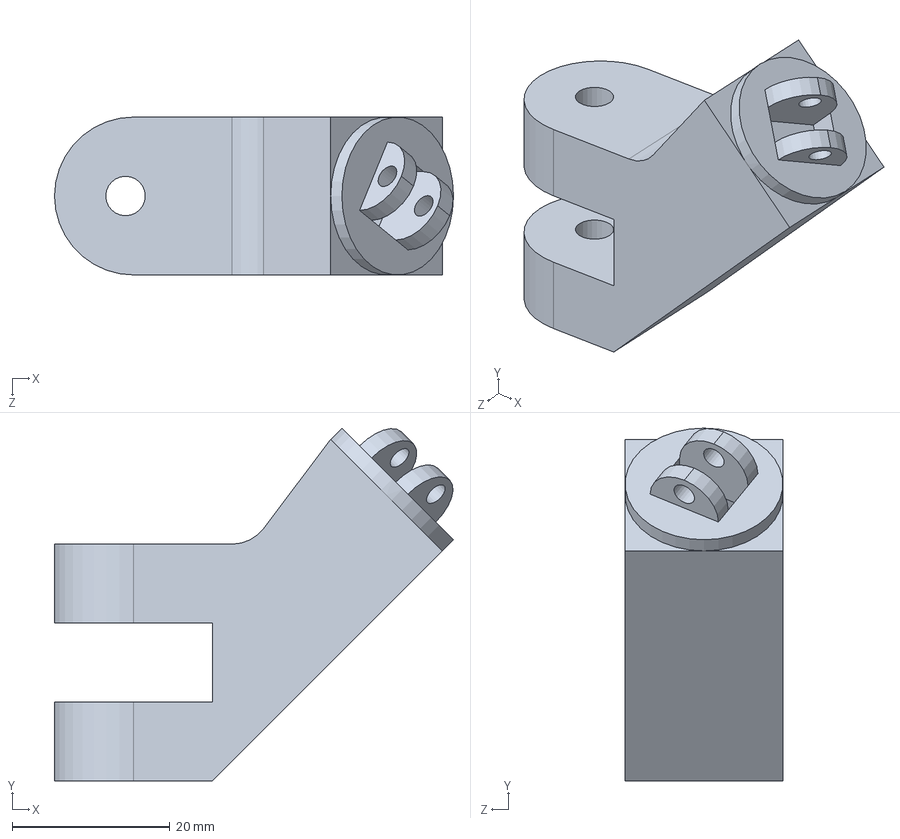
[picture p144: CAD file, 2022-01-19]
Design/Fingers/1stDigit/1.x/TBase1.2.SLDPRT
50.6 x 44.7 x 20.0 mm
