mustafab0/Bionic-Arm/Design/Fingers/2ndDigit/2.x/2.0/ITop2.0.SLDPRT

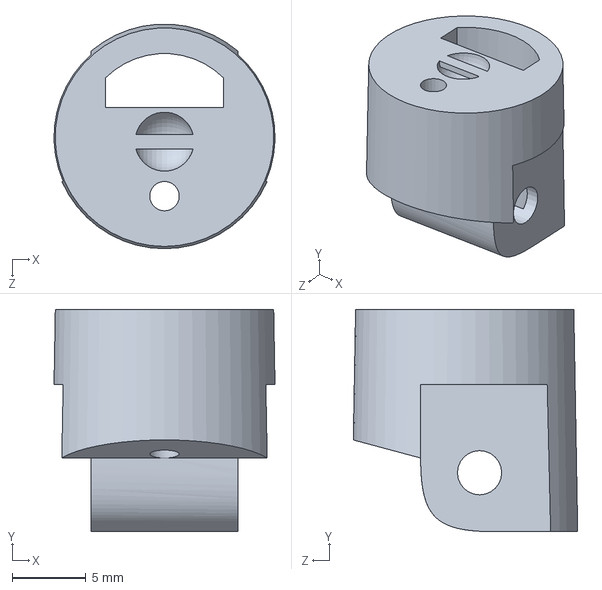
[picture p145: CAD file, 2022-01-19]
Design/Fingers/2ndDigit/2.x/2.0/ITop2.0.SLDPRT
15.0 x 15.1 x 15.2 mm
