mustafab0/Bionic-Arm/Design/Fingers/3rdDigit/2.x/2.0/mIntermediate2.0.SLDPRT

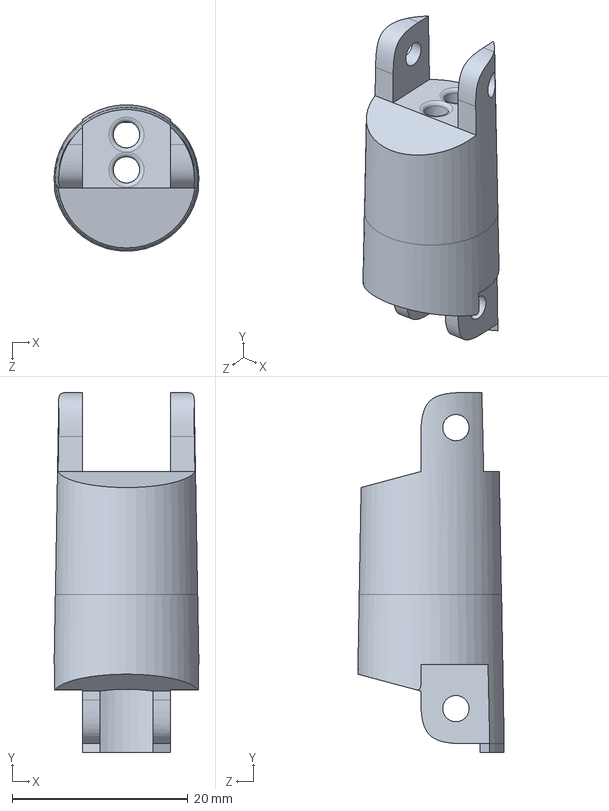
[picture p147: CAD file, 2022-01-19]
Design/Fingers/3rdDigit/2.x/2.0/mIntermediate2.0.SLDPRT
16.5 x 41.0 x 16.7 mm
