mustafab0/Bionic-Arm/Design/Fingers/4thDigit/1.x/RMid1.0.SLDPRT

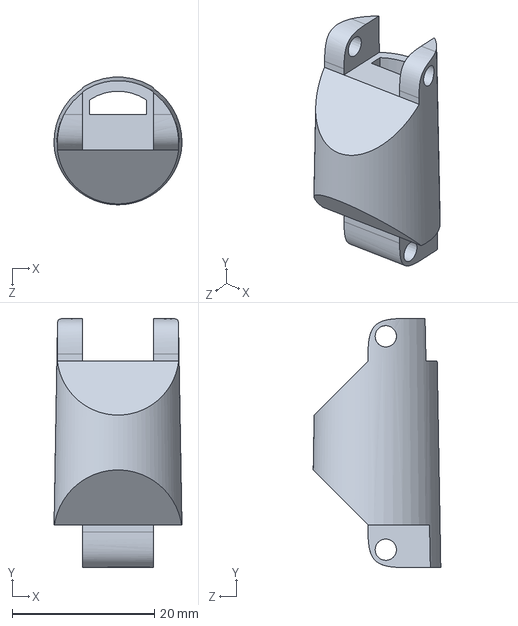
[picture p148: CAD file, 2022-01-19]
Design/Fingers/4thDigit/1.x/RMid1.0.SLDPRT
18.0 x 35.0 x 17.9 mm
