mustafab0/Bionic-Arm/Design/Fingers/4thDigit/2.x/2.0/rIntermediate2.0b.SLDPRT

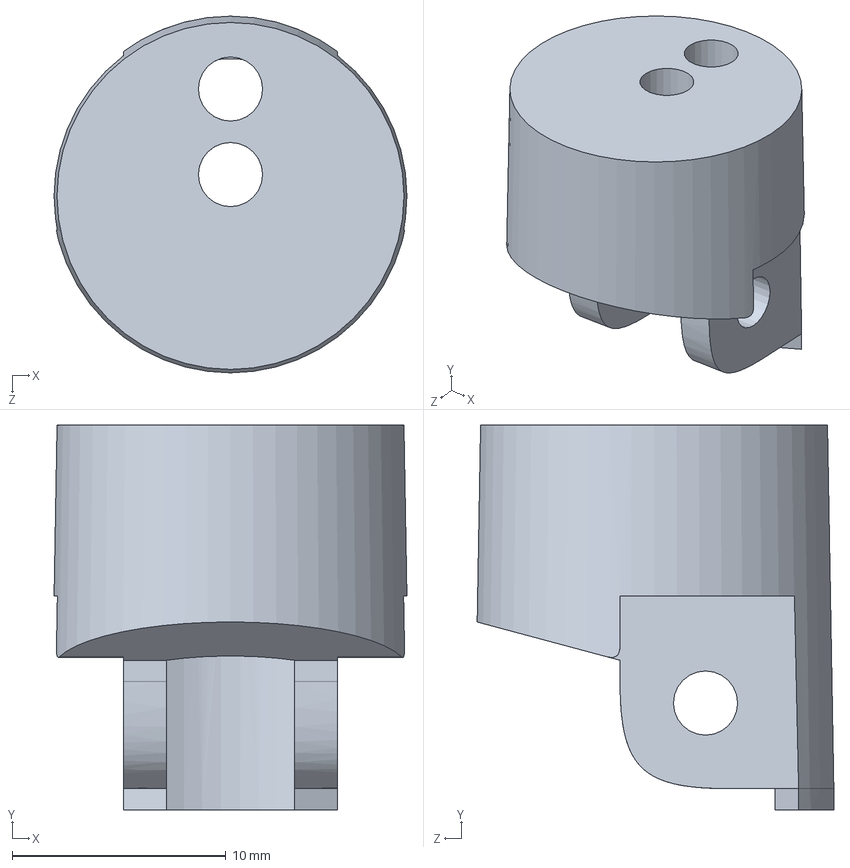
[picture p149: CAD file, 2022-01-19]
Design/Fingers/4thDigit/2.x/2.0/rIntermediate2.0b.SLDPRT
16.5 x 18.0 x 16.7 mm
