mustafab0/Bionic-Arm/Design/Fingers/5thDigit/1.x/PCap1.1.SLDPRT

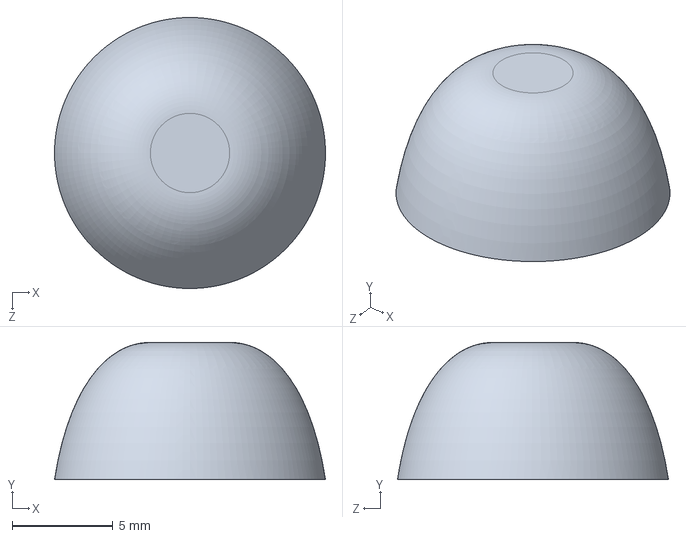
[picture p150: CAD file, 2022-01-19]
Design/Fingers/5thDigit/1.x/PCap1.1.SLDPRT
13.4 x 6.80 x 13.4 mm
