mustafab0/Bionic-Arm/Design/Fingers/5thDigit/2.x/pDistal2.0.SLDPRT

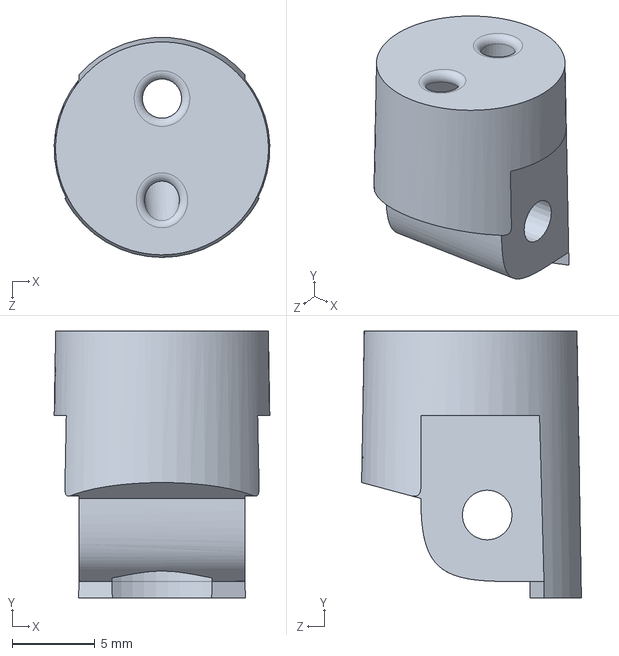
[picture p151: CAD file, 2022-01-19]
Design/Fingers/5thDigit/2.x/pDistal2.0.SLDPRT
13.0 x 16.1 x 13.2 mm
