mustafab0/Bionic-Arm/Design/Palm/2.x/2.1.x/Palmar2.1.sldprt

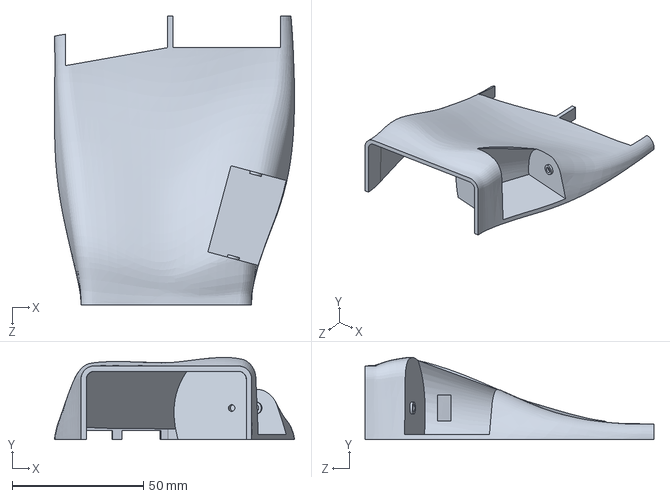
[picture p154: CAD file, 2022-01-19]
Design/Palm/2.x/2.1.x/Palmar2.1.sldprt
91.4 x 31.3 x 110.0 mm
