mustafab0/Bionic-Arm/Design/Final/mini-dc-geared-motor-1.snapshot.2/DC_GE_RED_Motor_02.SLDPRT

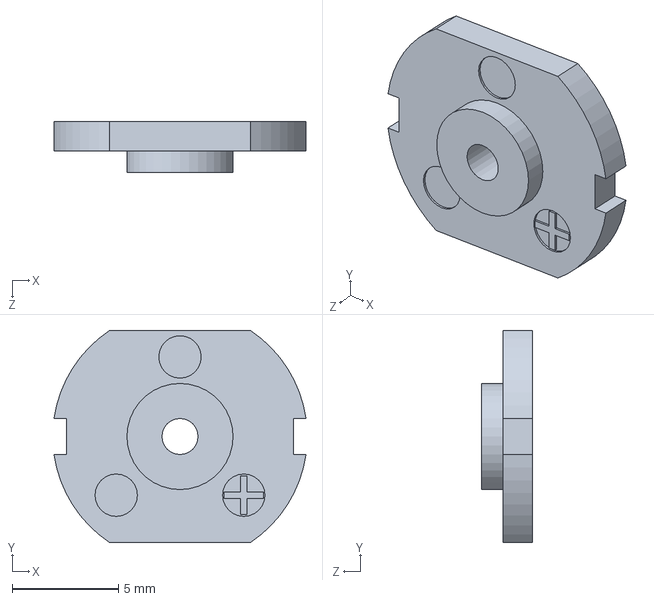
[picture p155: CAD file, 2022-01-19]
Design/Final/mini-dc-geared-motor-1.snapshot.2/DC_GE_RED_Motor_02.SLDPRT
11.9 x 10.0 x 2.40 mm
