mustafab0/Bionic-Arm/Design/Fingers/1stDigit/1.x/TBase1.1.SLDPRT

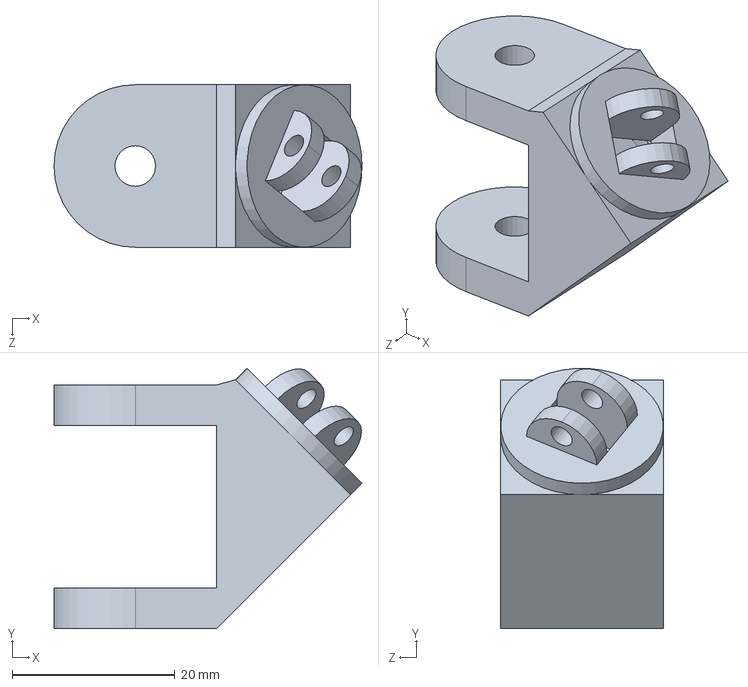
[picture p156: CAD file, 2022-01-19]
Design/Fingers/1stDigit/1.x/TBase1.1.SLDPRT
37.9 x 32.0 x 20.0 mm
