mustafab0/Bionic-Arm/Design/Fingers/2ndDigit/2.x/2.0/UpperMid2.0.sldprt

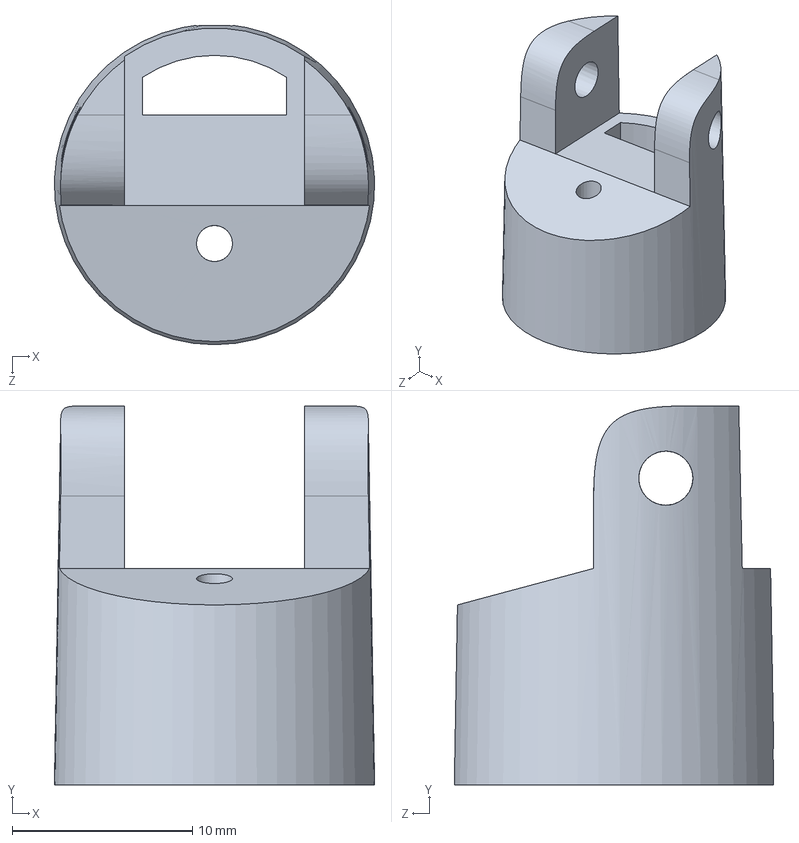
[picture p157: CAD file, 2022-01-19]
Design/Fingers/2ndDigit/2.x/2.0/UpperMid2.0.sldprt
17.7 x 21.0 x 17.7 mm
