mustafab0/Bionic-Arm/Design/Fingers/2ndDigit/2.x/2.1/iDistal2.1.SLDPRT

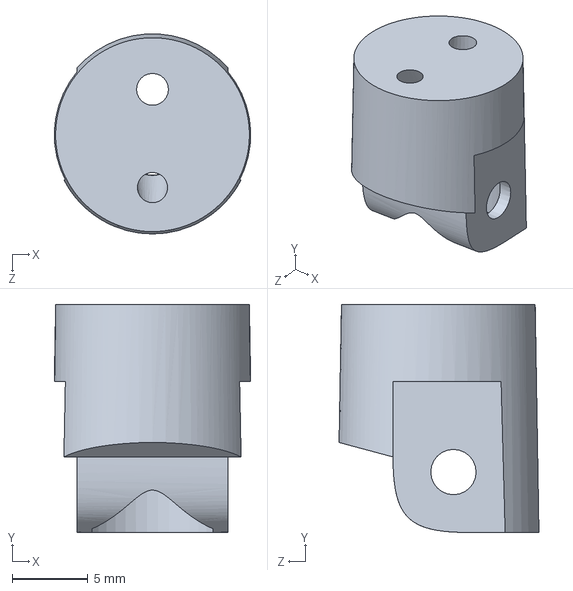
[picture p158: CAD file, 2022-01-19]
Design/Fingers/2ndDigit/2.x/2.1/iDistal2.1.SLDPRT
13.0 x 15.1 x 13.2 mm
