mustafab0/Bionic-Arm/Design/Fingers/3rdDigit/1.x/MMid1.0.SLDPRT

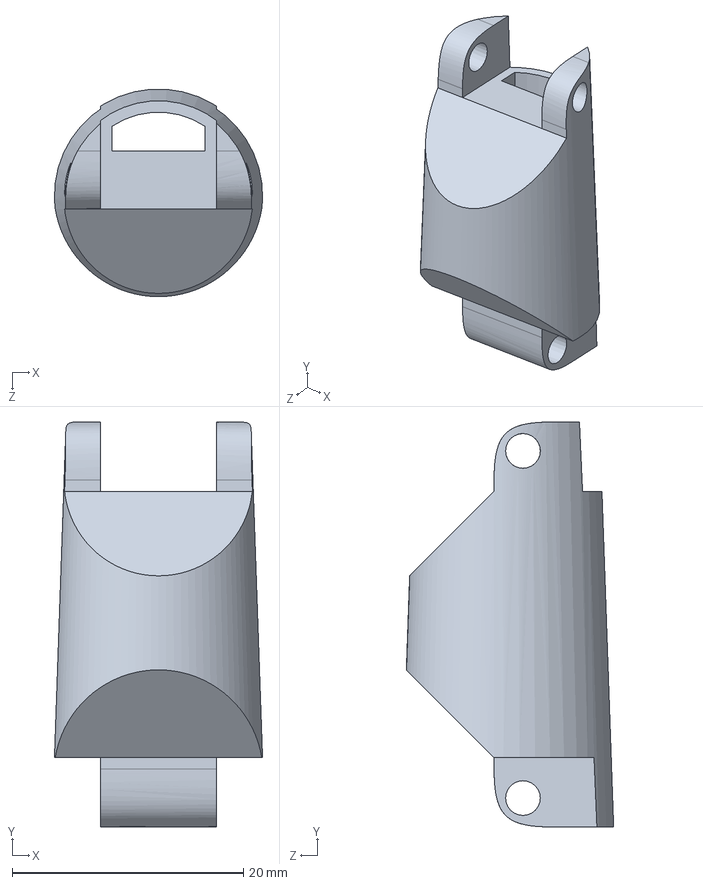
[picture p159: CAD file, 2022-01-19]
Design/Fingers/3rdDigit/1.x/MMid1.0.SLDPRT
18.0 x 35.0 x 17.9 mm
