mustafab0/Bionic-Arm/Design/Fingers/3rdDigit/2.x/2.0/mProximal2.0b.SLDPRT

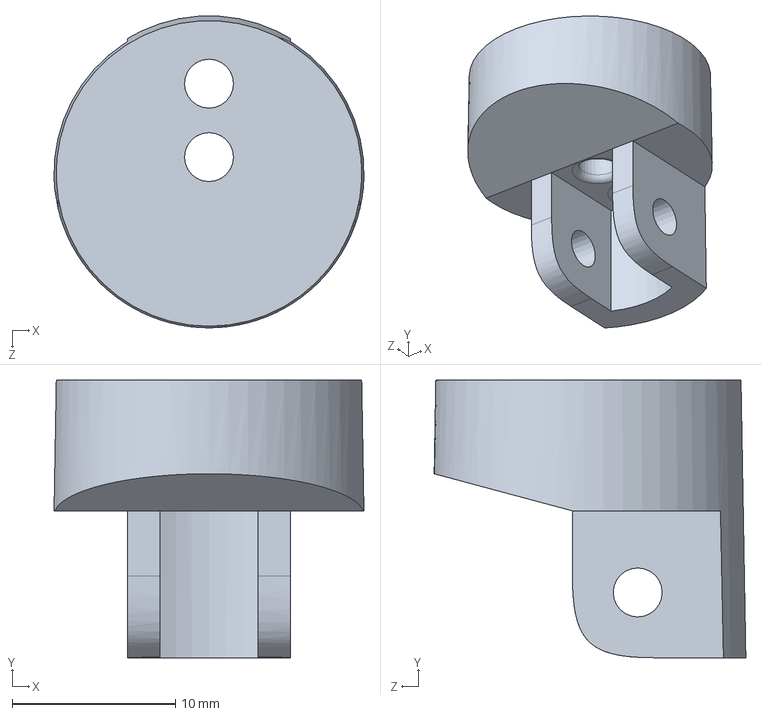
[picture p160: CAD file, 2022-01-19]
Design/Fingers/3rdDigit/2.x/2.0/mProximal2.0b.SLDPRT
19.0 x 17.0 x 19.1 mm
