mustafab0/Bionic-Arm/Design/Fingers/4thDigit/1.x/RCap1.0.SLDPRT

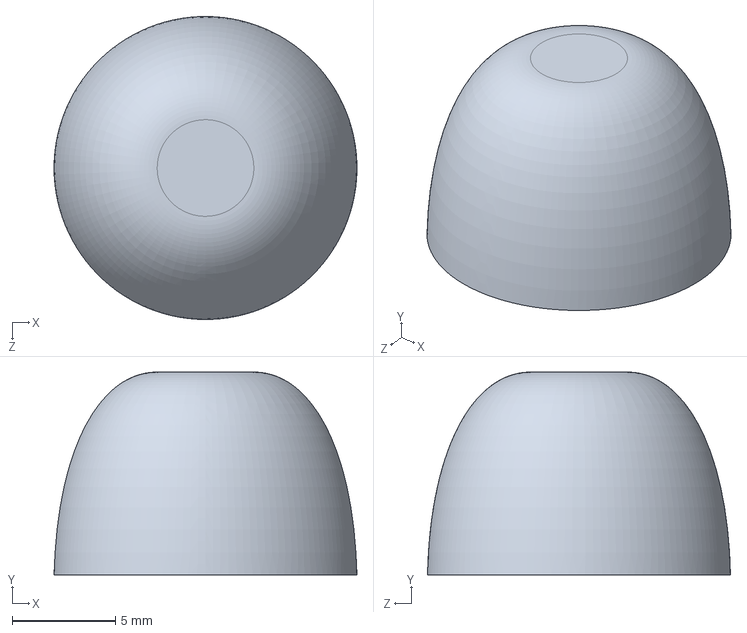
[picture p161: CAD file, 2022-01-19]
Design/Fingers/4thDigit/1.x/RCap1.0.SLDPRT
14.7 x 9.83 x 14.7 mm
