mustafab0/Bionic-Arm/Design/Fingers/4thDigit/2.x/2.0/rProximal2.0.SLDPRT

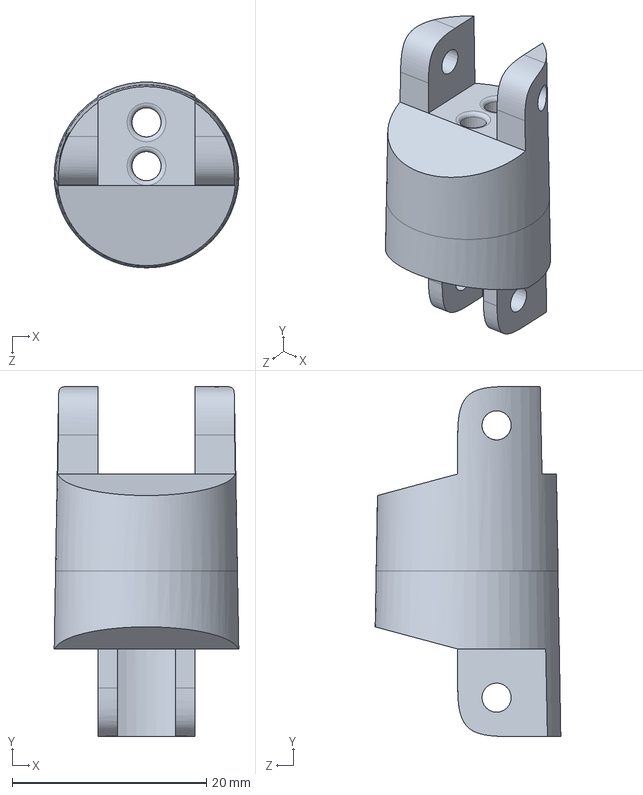
[picture p162: CAD file, 2022-01-19]
Design/Fingers/4thDigit/2.x/2.0/rProximal2.0.SLDPRT
19.0 x 36.0 x 19.1 mm
