mustafab0/Bionic-Arm/Design/Fingers/5thDigit/1.x/PMid1.1.SLDPRT

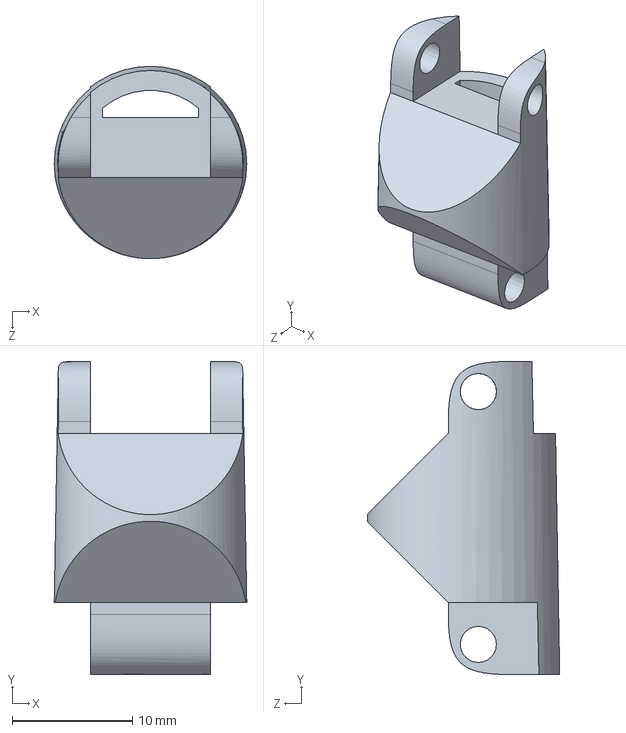
[picture p163: CAD file, 2022-01-19]
Design/Fingers/5thDigit/1.x/PMid1.1.SLDPRT
16.0 x 26.0 x 16.0 mm
