mustafab0/Bionic-Arm/Design/Fingers/5thDigit/2.x/pIntermediate2.0b.SLDPRT

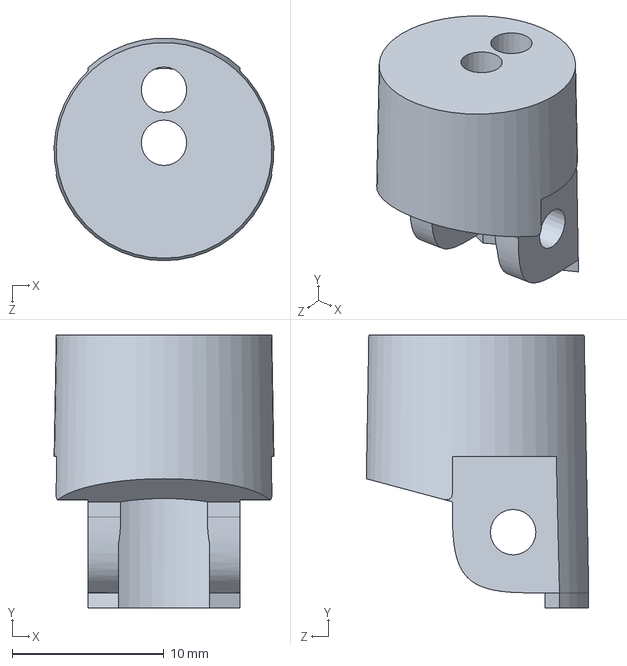
[picture p164: CAD file, 2022-01-19]
Design/Fingers/5thDigit/2.x/pIntermediate2.0b.SLDPRT
14.5 x 18.0 x 14.7 mm
