mustafab0/Bionic-Arm/Design/Palm/2.x/2.0.x/Palm2.0.SLDPRT

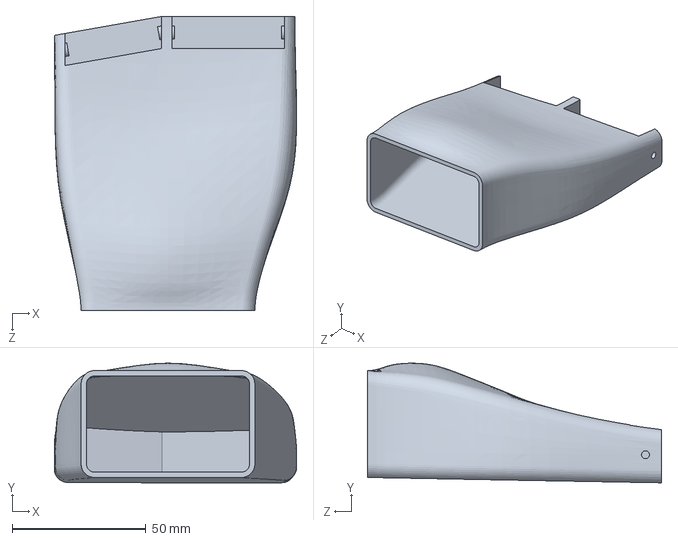
[picture p166: CAD file, 2022-01-19]
Design/Palm/2.x/2.0.x/Palm2.0.SLDPRT
90.7 x 44.8 x 110.0 mm
