mustafab0/Bionic-Arm/Design/Palm/2.x/2.1.x/Palm2.1.SLDPRT

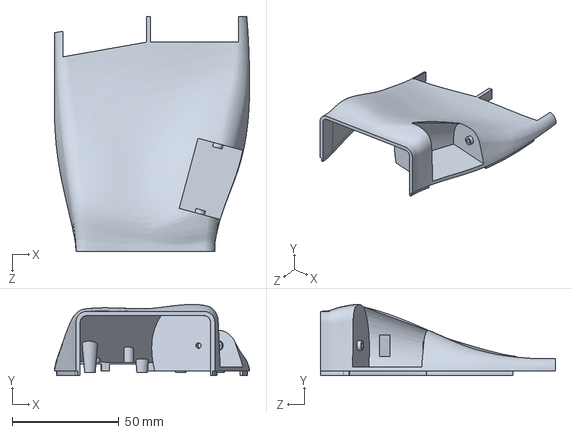
[picture p167: CAD file, 2022-01-19]
Design/Palm/2.x/2.1.x/Palm2.1.SLDPRT
91.4 x 33.3 x 110.0 mm
