mustafab0/Bionic-Arm/Design/Final/Pulley Gear Shaft.SLDPRT

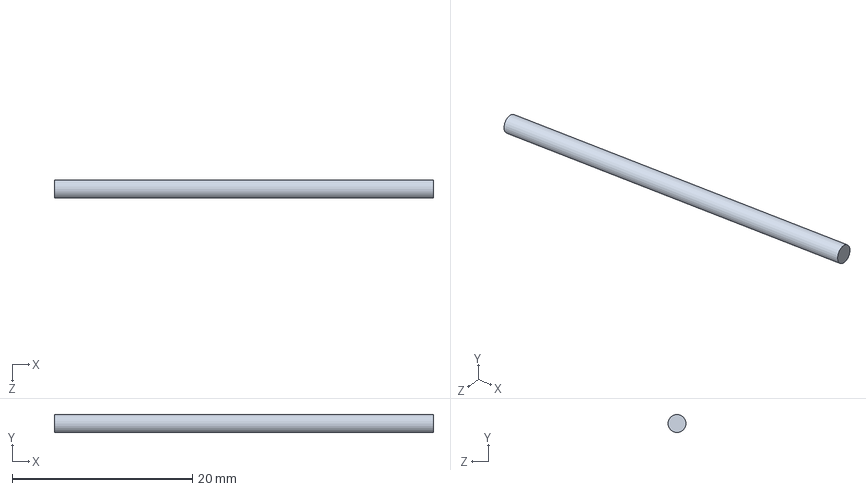
[picture p168: CAD file, 2022-01-19]
Design/Final/Pulley Gear Shaft.SLDPRT
42.0 x 2.00 x 2.00 mm
