mustafab0/Bionic-Arm/Design/Fingers/1stDigit/1.x/Pin.SLDPRT

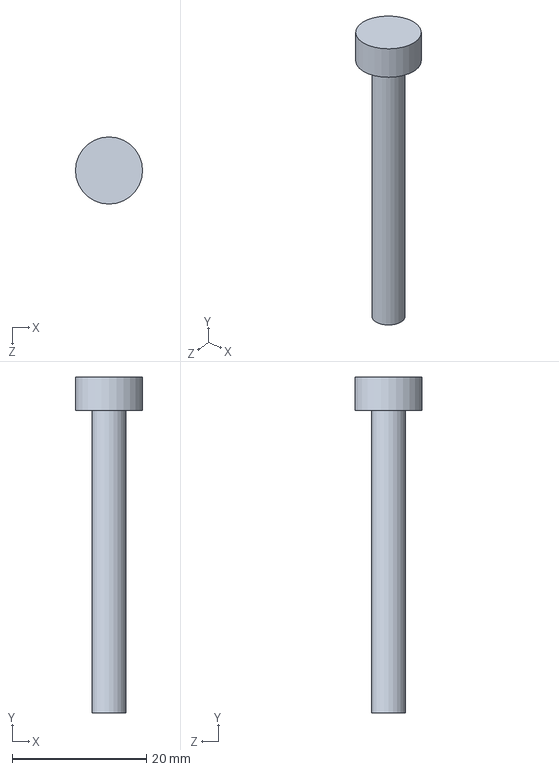
[picture p169: CAD file, 2022-01-19]
Design/Fingers/1stDigit/1.x/Pin.SLDPRT
10.0 x 50.0 x 10.0 mm
