mustafab0/Bionic-Arm/Design/Fingers/1stDigit/2.x/tProximal2.2.SLDPRT

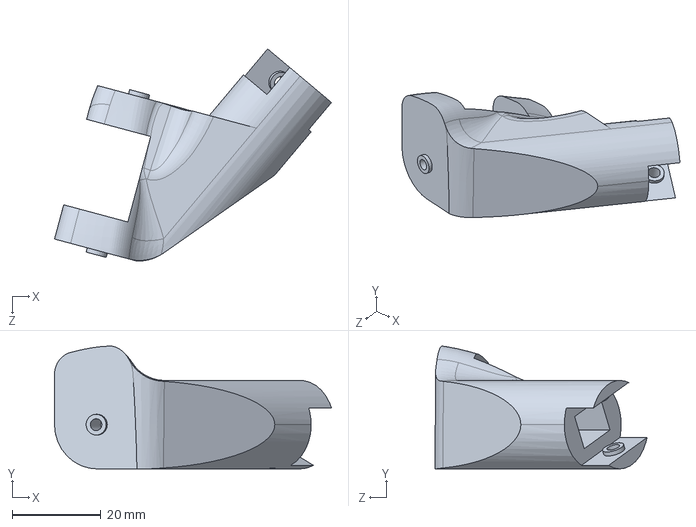
[picture p170: CAD file, 2022-01-19]
Design/Fingers/1stDigit/2.x/tProximal2.2.SLDPRT
62.6 x 27.7 x 47.9 mm
