mustafab0/Bionic-Arm/Design/Fingers/2ndDigit/2.x/2.1/iProximal2.1.SLDPRT

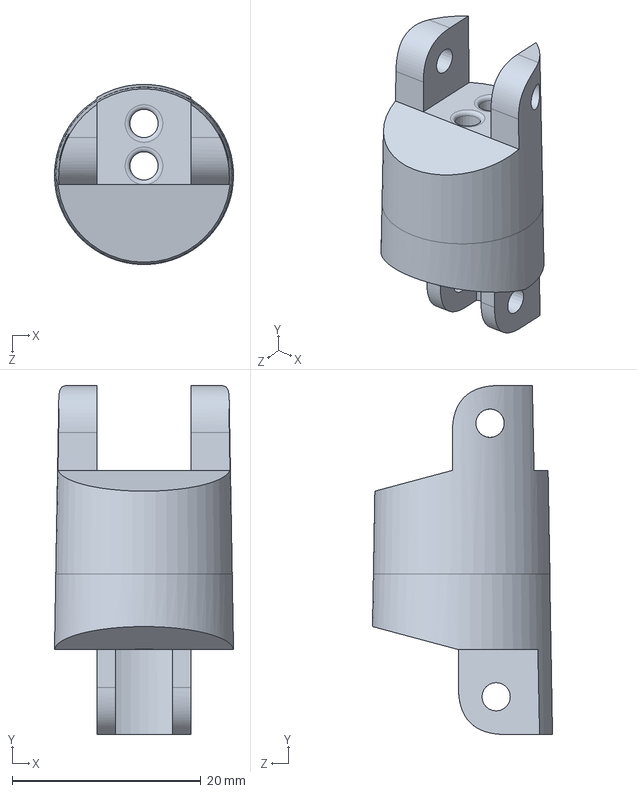
[picture p171: CAD file, 2022-01-19]
Design/Fingers/2ndDigit/2.x/2.1/iProximal2.1.SLDPRT
19.0 x 37.0 x 19.1 mm
