mustafab0/Bionic-Arm/Design/Fingers/4thDigit/1.x/RBase1.0.SLDPRT

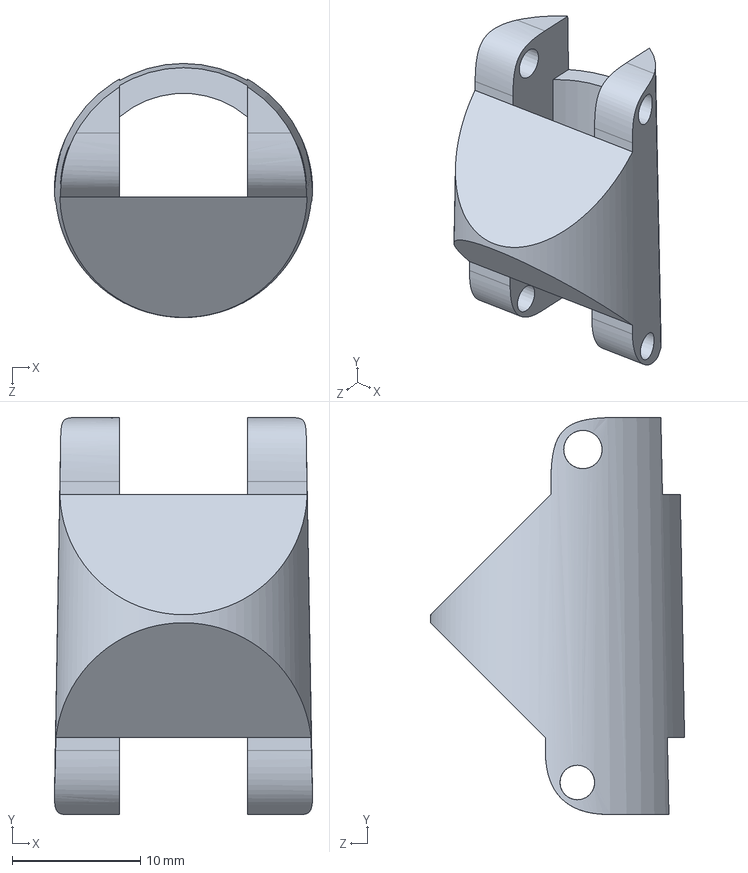
[picture p172: CAD file, 2022-01-19]
Design/Fingers/4thDigit/1.x/RBase1.0.SLDPRT
20.2 x 31.0 x 19.8 mm
