mustafab0/Bionic-Arm/Design/Fingers/4thDigit/2.x/2.0/rDistal2.0.SLDPRT

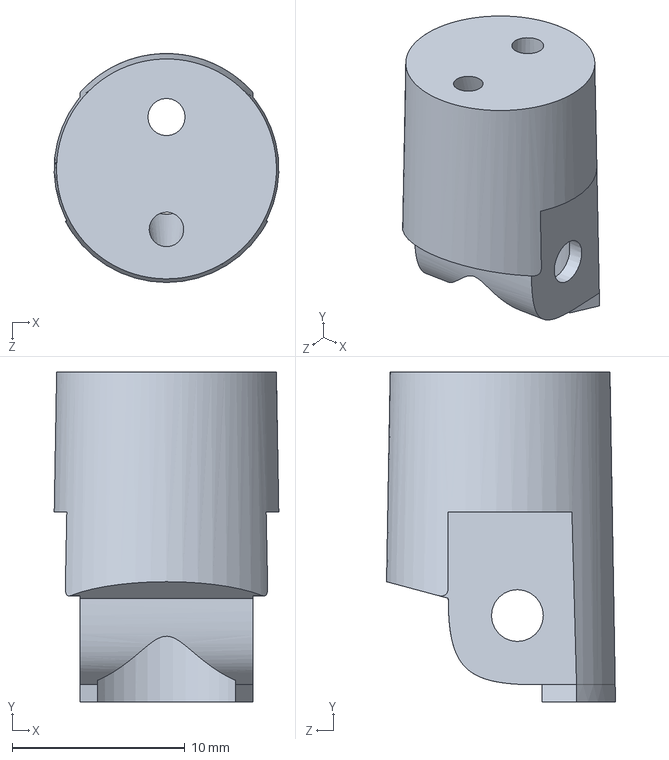
[picture p173: CAD file, 2022-01-19]
Design/Fingers/4thDigit/2.x/2.0/rDistal2.0.SLDPRT
13.0 x 19.1 x 13.2 mm
