mustafab0/Bionic-Arm/Design/Fingers/5thDigit/1.x/PTop1.1.SLDPRT

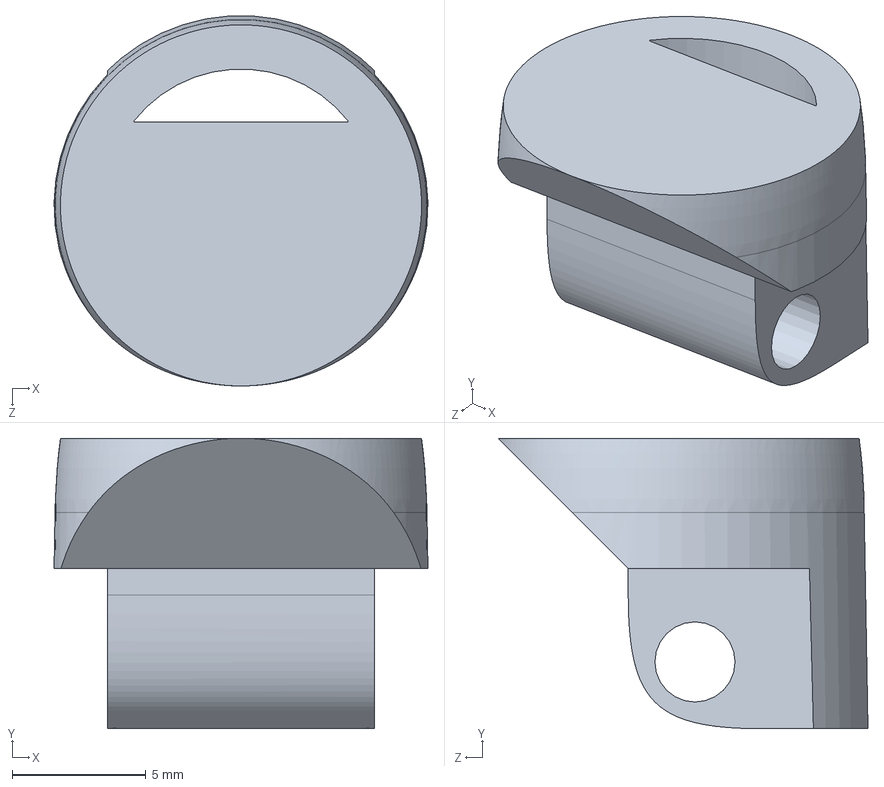
[picture p174: CAD file, 2022-01-19]
Design/Fingers/5thDigit/1.x/PTop1.1.SLDPRT
14.0 x 10.9 x 13.9 mm
