mustafab0/Bionic-Arm/Design/Fingers/5thDigit/2.x/pMetaCarpal2.0.SLDPRT

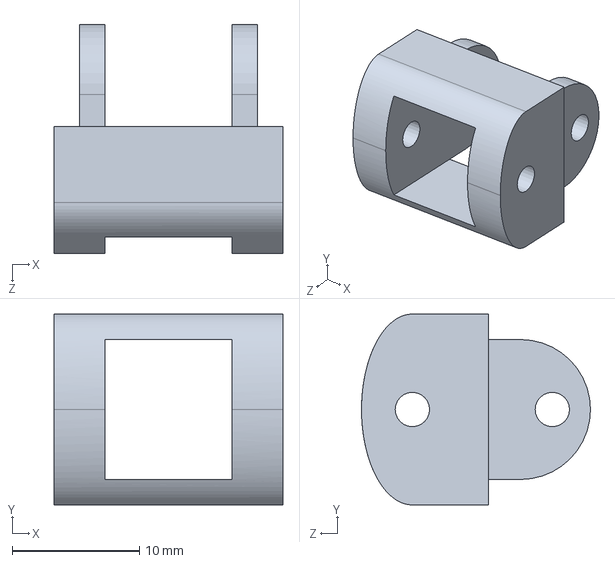
[picture p175: CAD file, 2022-01-19]
Design/Fingers/5thDigit/2.x/pMetaCarpal2.0.SLDPRT
18.0 x 15.0 x 18.0 mm
