mustafab0/Bionic-Arm/Design/Palm/2.x/2.0.x/PalmarSide2.0.2.sldprt

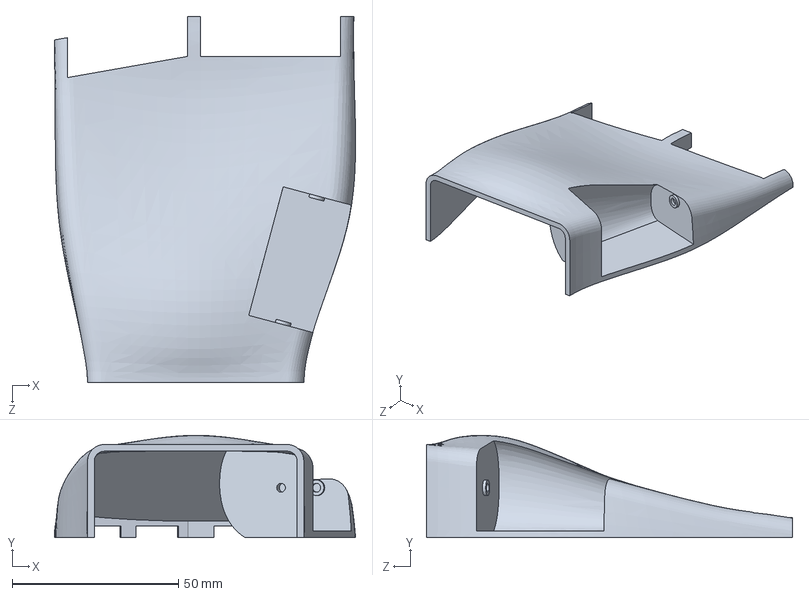
[picture p177: CAD file, 2022-01-19]
Design/Palm/2.x/2.0.x/PalmarSide2.0.2.sldprt
90.5 x 30.7 x 110.0 mm
