mustafab0/Bionic-Arm/Design/Palm/2.x/2.1.x/Dorsal2.1.sldprt

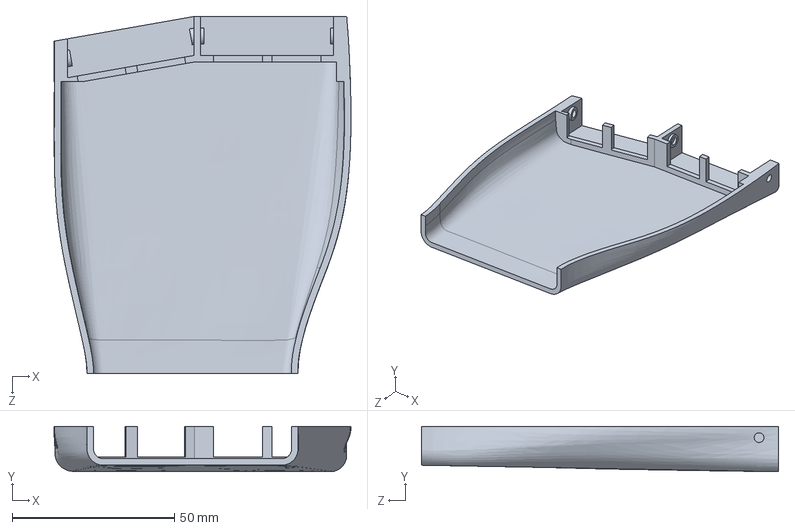
[picture p178: CAD file, 2022-01-19]
Design/Palm/2.x/2.1.x/Dorsal2.1.sldprt
91.5 x 14.0 x 110.0 mm
