mustafab0/Bionic-Arm/Design/Final/mini-dc-geared-motor-1.snapshot.2/DC_GE_RED_Motor_04.SLDPRT

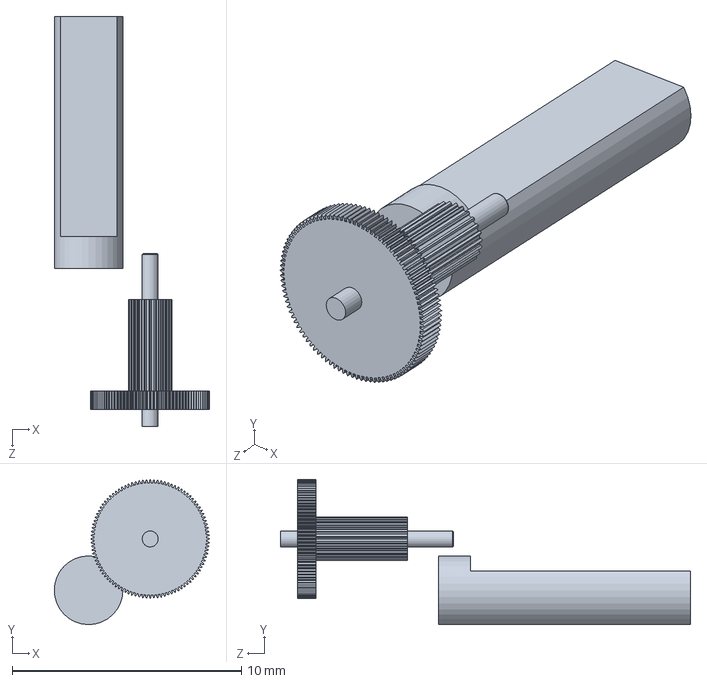
[picture p179: CAD file, 2022-01-19]
Design/Final/mini-dc-geared-motor-1.snapshot.2/DC_GE_RED_Motor_04.SLDPRT
6.79 x 6.34 x 17.9 mm
