mustafab0/Bionic-Arm/Design/Final/Worm.SLDPRT

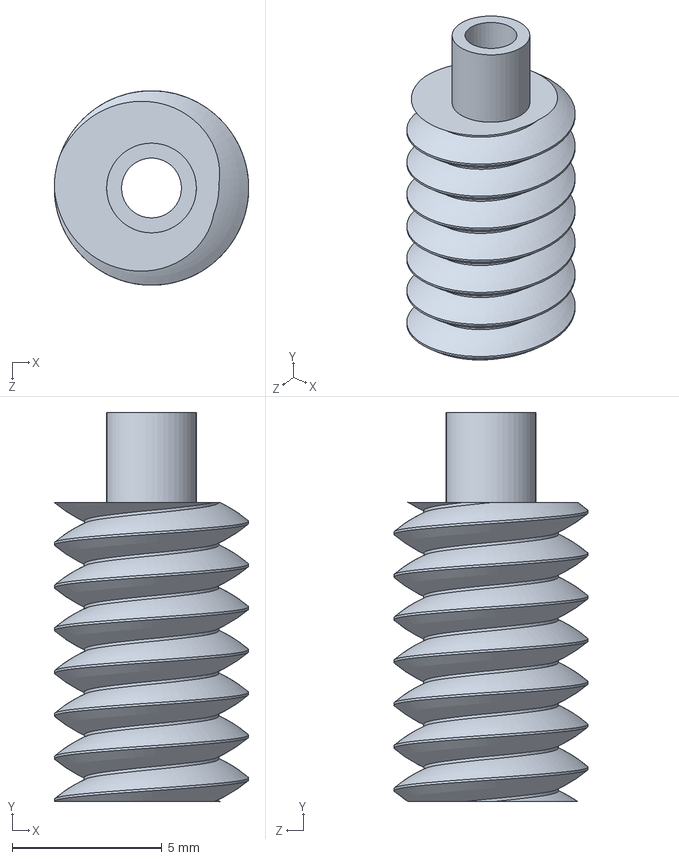
[picture p180: CAD file, 2022-01-19]
Design/Final/Worm.SLDPRT
6.50 x 13.0 x 6.50 mm
