mustafab0/Bionic-Arm/Design/Fingers/1stDigit/2.x/tDistal2.0.SLDPRT

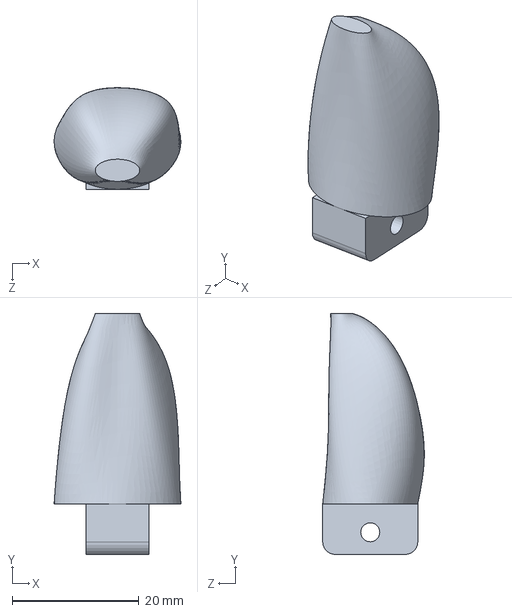
[picture p181: CAD file, 2022-01-19]
Design/Fingers/1stDigit/2.x/tDistal2.0.SLDPRT
20.0 x 38.0 x 16.0 mm
