mustafab0/Bionic-Arm/Design/Fingers/2ndDigit/1.x/ICap1.3.SLDPRT

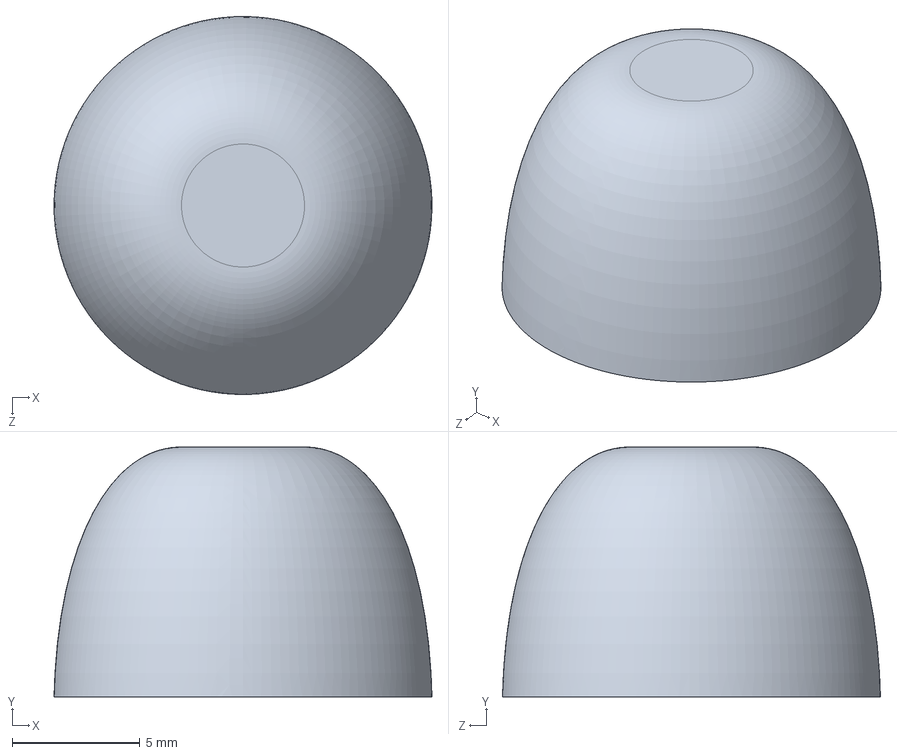
[picture p182: CAD file, 2022-01-19]
Design/Fingers/2ndDigit/1.x/ICap1.3.SLDPRT
14.8 x 9.80 x 14.8 mm
