mustafab0/Bionic-Arm/Design/Fingers/2ndDigit/2.x/2.0/LowerBase2.0.sldprt

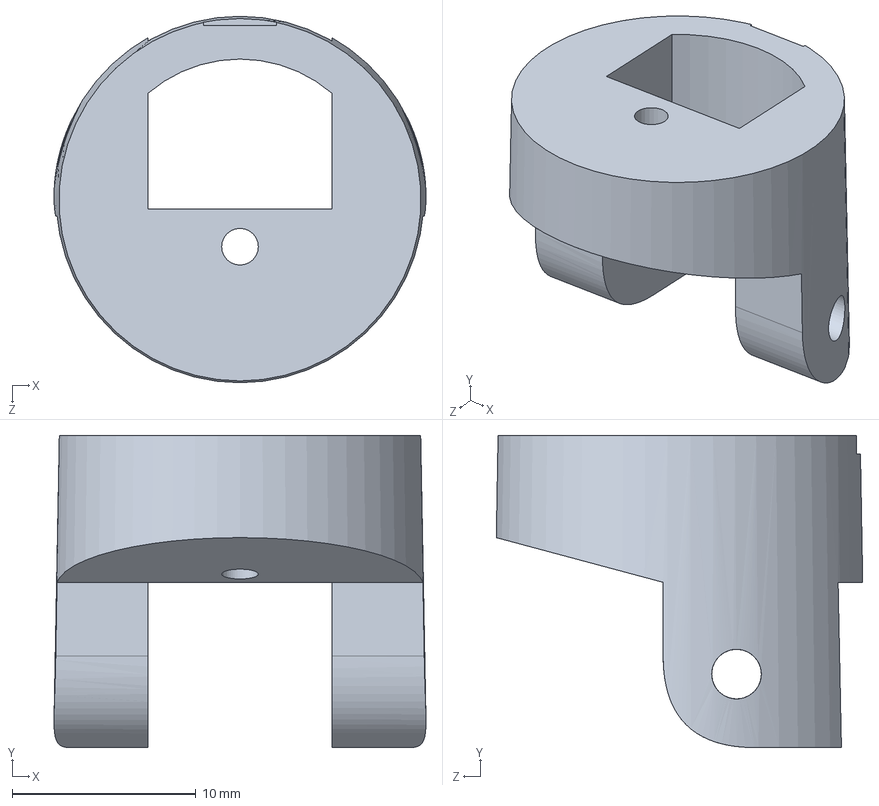
[picture p183: CAD file, 2022-01-19]
Design/Fingers/2ndDigit/2.x/2.0/LowerBase2.0.sldprt
20.3 x 17.0 x 20.0 mm
