mustafab0/Bionic-Arm/Design/Fingers/2ndDigit/2.x/2.1/iMetaCarpal2.1.SLDPRT

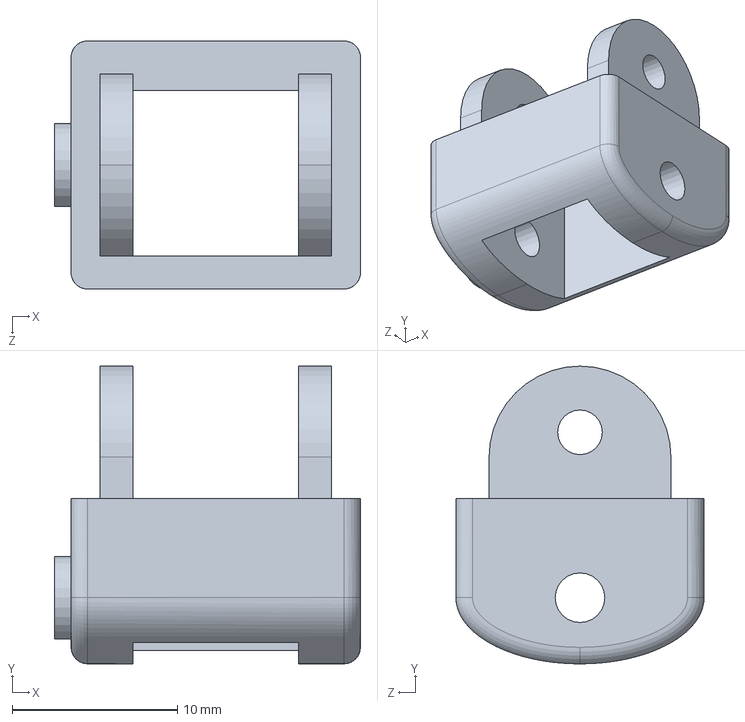
[picture p184: CAD file, 2022-01-19]
Design/Fingers/2ndDigit/2.x/2.1/iMetaCarpal2.1.SLDPRT
18.5 x 18.0 x 15.0 mm
