mustafab0/Bionic-Arm/Design/Fingers/4thDigit/1.x/RTop1.0.STL

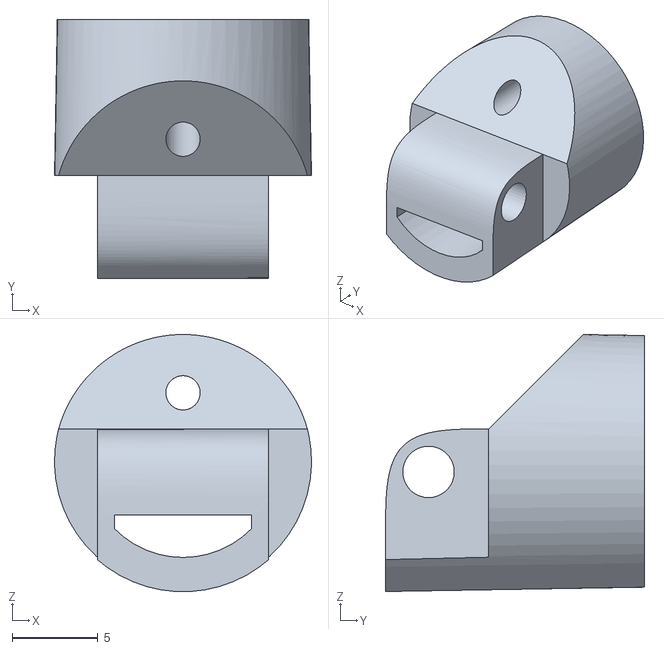
[picture p185: CAD file, 2022-01-19]
Design/Fingers/4thDigit/1.x/RTop1.0.STL
15.0 x 15.1 x 15.0
