mustafab0/Bionic-Arm/Design/Fingers/5thDigit/1.x/PMid1.0.SLDPRT

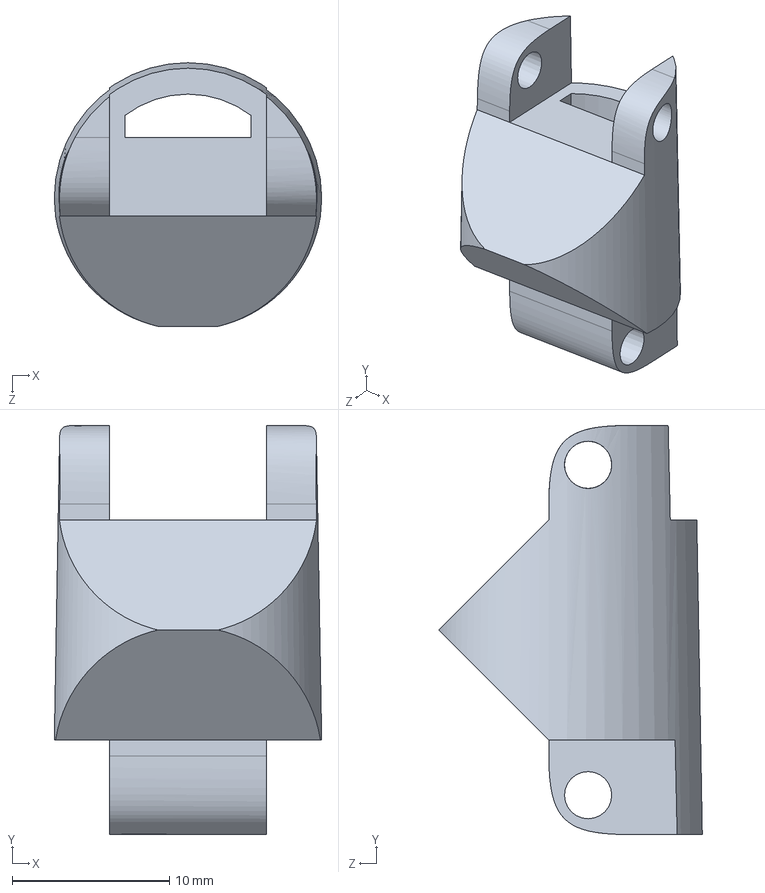
[picture p186: CAD file, 2022-01-19]
Design/Fingers/5thDigit/1.x/PMid1.0.SLDPRT
17.0 x 26.0 x 16.8 mm
