mustafab0/Bionic-Arm/Design/Final/Pulley2.0.SLDPRT

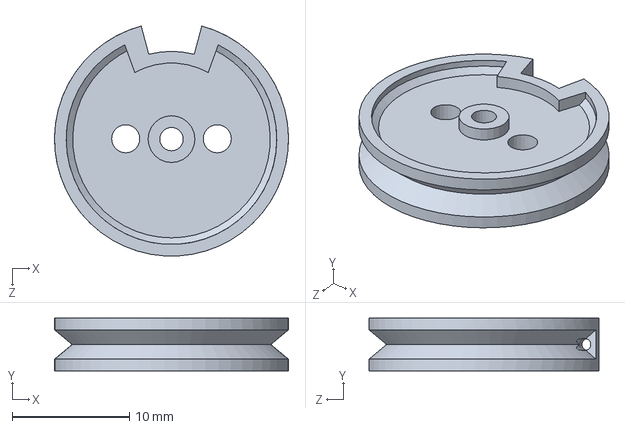
[picture p189: CAD file, 2022-01-19]
Design/Final/Pulley2.0.SLDPRT
20.0 x 4.50 x 19.6 mm
