mustafab0/Bionic-Arm/Design/Fingers/1stDigit/1.x/TTop1.0.SLDPRT

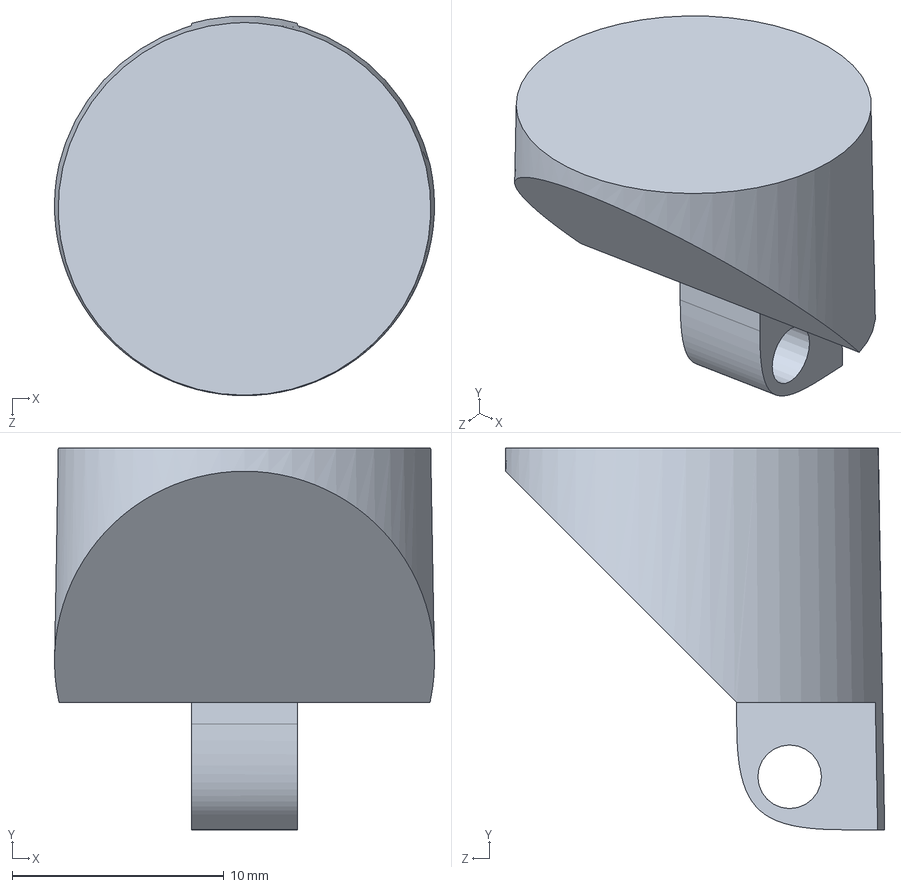
[picture p190: CAD file, 2022-01-19]
Design/Fingers/1stDigit/1.x/TTop1.0.SLDPRT
17.9 x 18.0 x 17.9 mm
