mustafab0/Bionic-Arm/Design/Fingers/2ndDigit/2.x/2.0/Stand.SLDPRT

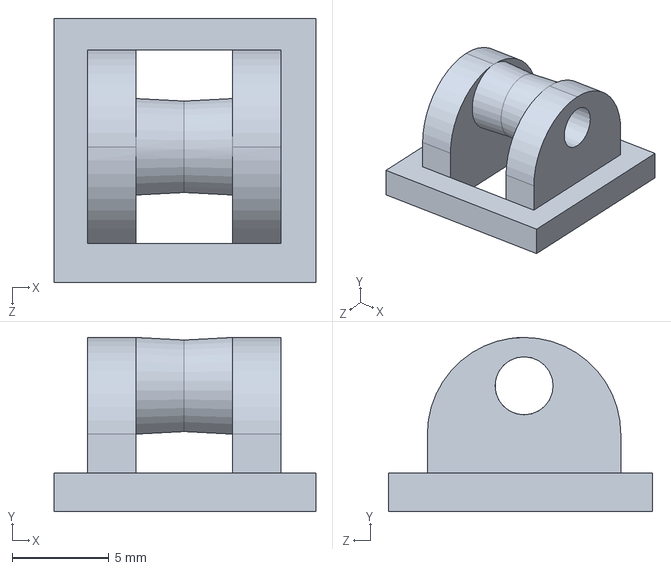
[picture p191: CAD file, 2022-01-19]
Design/Fingers/2ndDigit/2.x/2.0/Stand.SLDPRT
13.5 x 9.00 x 13.6 mm
