mustafab0/Bionic-Arm/Design/Fingers/2ndDigit/2.x/2.1/iIntermediate2.1a.SLDPRT

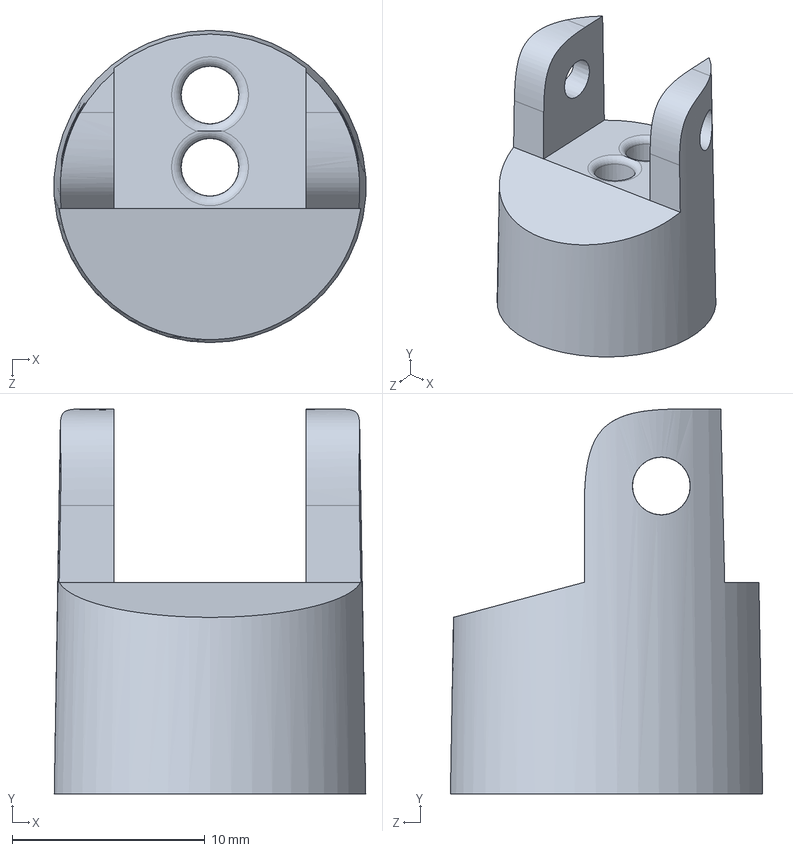
[picture p192: CAD file, 2022-01-19]
Design/Fingers/2ndDigit/2.x/2.1/iIntermediate2.1a.SLDPRT
16.2 x 20.0 x 16.2 mm
