mustafab0/Bionic-Arm/Design/Fingers/3rdDigit/1.x/MTop1.1.SLDPRT

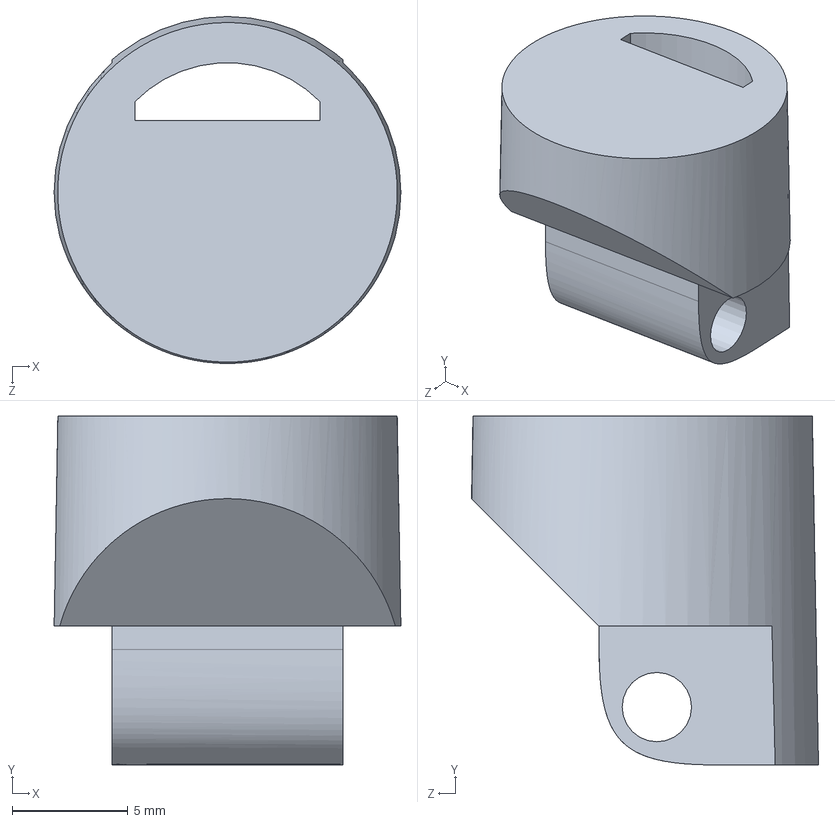
[picture p193: CAD file, 2022-01-19]
Design/Fingers/3rdDigit/1.x/MTop1.1.SLDPRT
15.0 x 15.1 x 15.0 mm
