mustafab0/Bionic-Arm/Design/Fingers/5thDigit/1.x/PTop1.0.SLDPRT

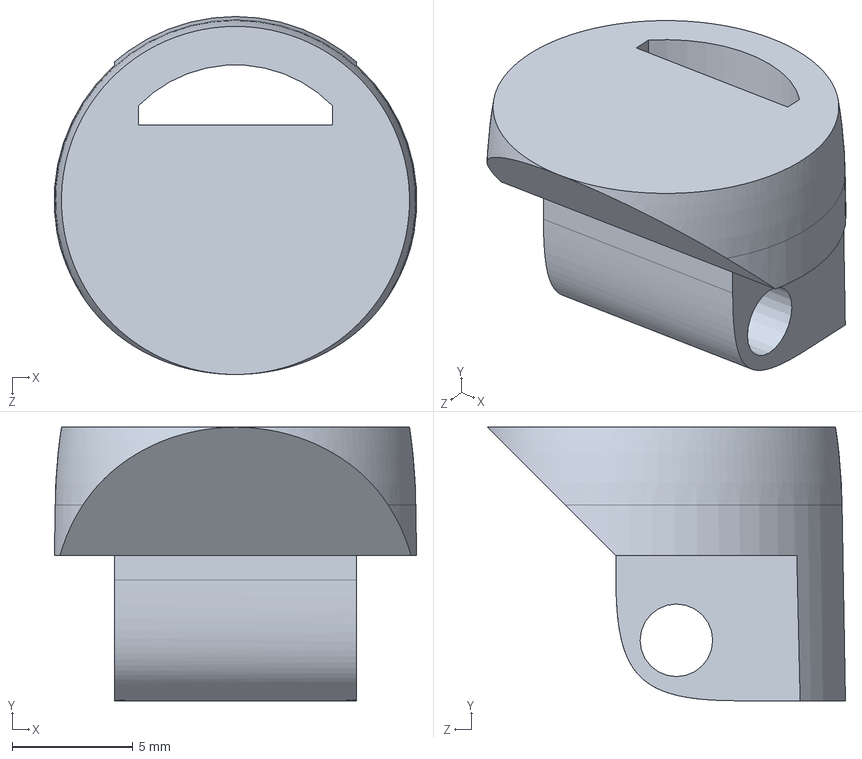
[picture p194: CAD file, 2022-01-19]
Design/Fingers/5thDigit/1.x/PTop1.0.SLDPRT
15.0 x 11.3 x 14.8 mm
