mustafab0/Bionic-Arm/Design/Fingers/5thDigit/2.x/pIntermediate2.0a.SLDPRT

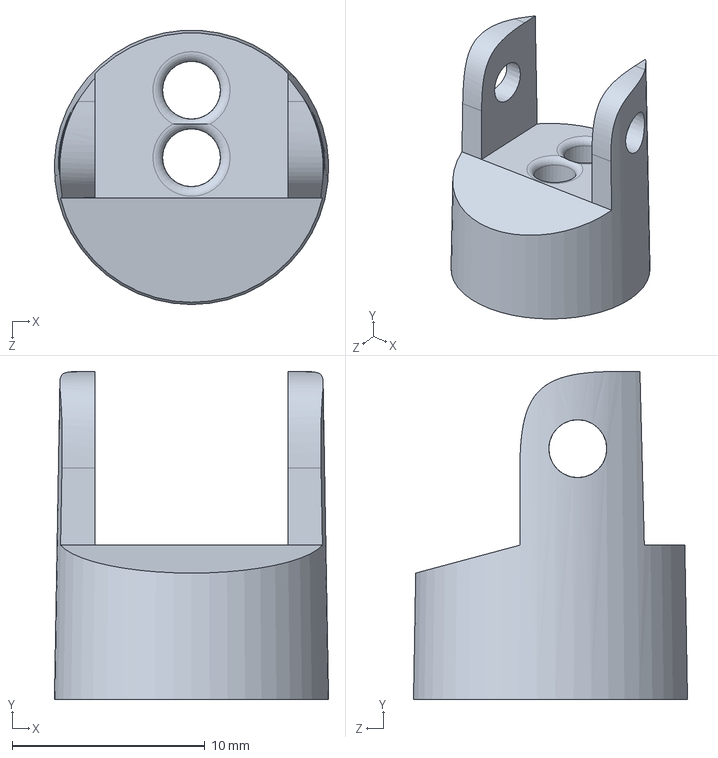
[picture p195: CAD file, 2022-01-19]
Design/Fingers/5thDigit/2.x/pIntermediate2.0a.SLDPRT
14.2 x 17.0 x 14.2 mm
