mustafab0/Bionic-Arm/Design/Palm/2.x/2.0.x/PalmarSide2.0.2beta.sldprt

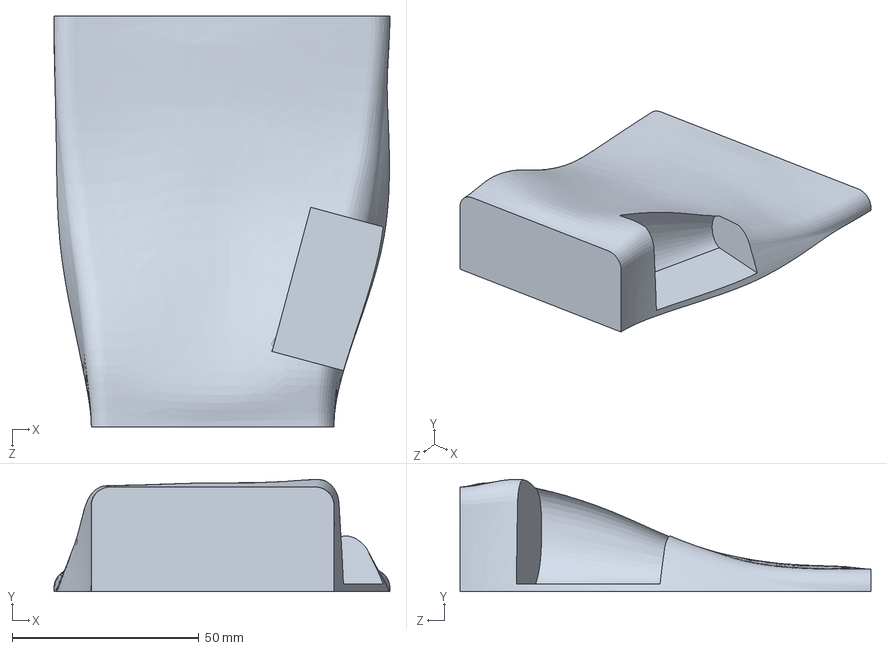
[picture p196: CAD file, 2022-01-19]
Design/Palm/2.x/2.0.x/PalmarSide2.0.2beta.sldprt
90.0 x 30.0 x 110.0 mm
