mustafab0/Bionic-Arm/Design/Final/Support.SLDPRT

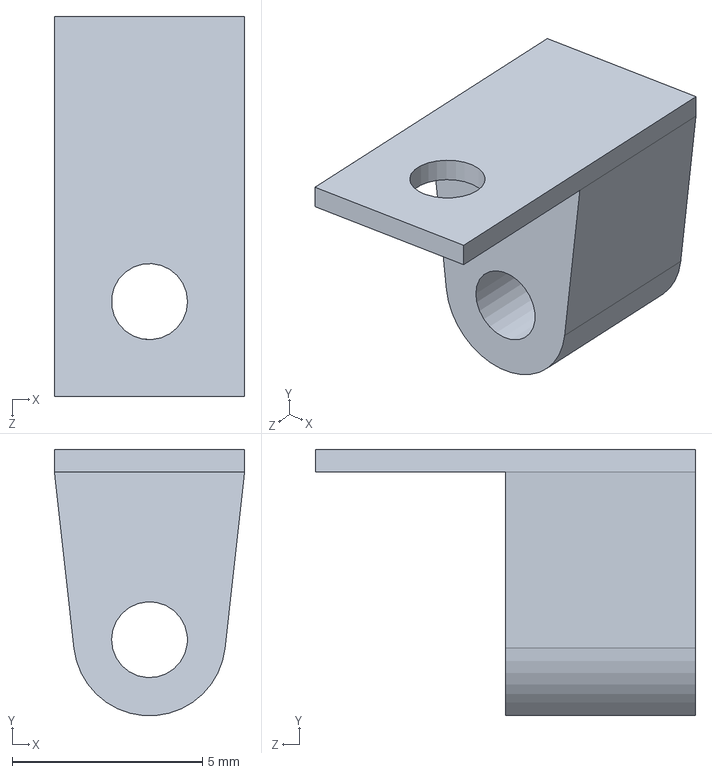
[picture p197: CAD file, 2022-01-19]
Design/Final/Support.SLDPRT
5.00 x 6.99 x 10.0 mm
