mustafab0/Bionic-Arm/Design/Fingers/1stDigit/1.x/TBase1.0.SLDPRT

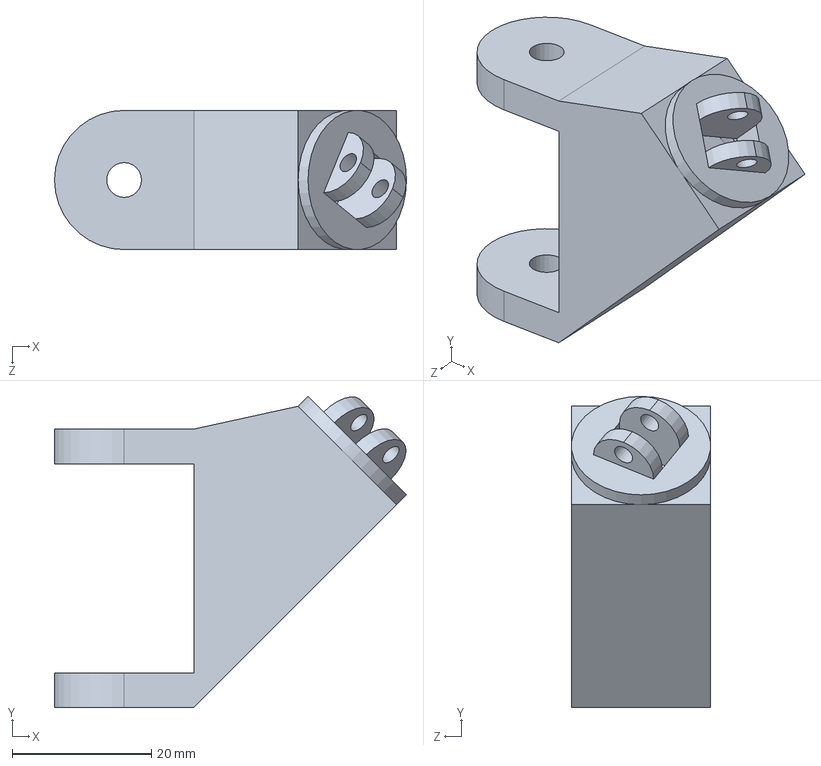
[picture p198: CAD file, 2022-01-19]
Design/Fingers/1stDigit/1.x/TBase1.0.SLDPRT
50.6 x 44.7 x 20.0 mm
