mustafab0/Bionic-Arm/Design/Fingers/1stDigit/2.x/tProximal2.0.SLDPRT

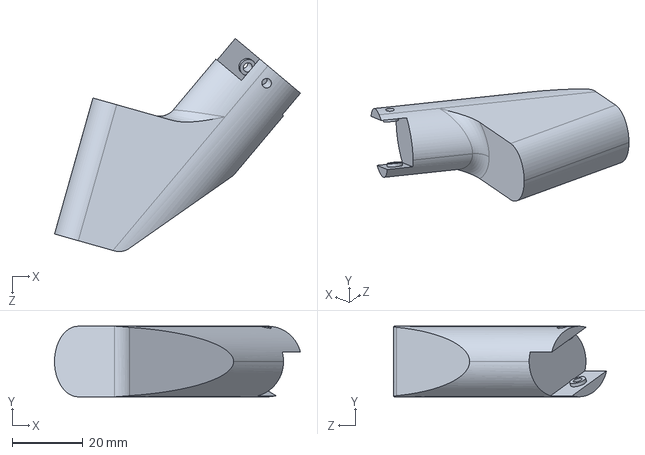
[picture p199: CAD file, 2022-01-19]
Design/Fingers/1stDigit/2.x/tProximal2.0.SLDPRT
69.6 x 20.0 x 60.3 mm
