mustafab0/Bionic-Arm/Design/Fingers/3rdDigit/1.x/MBase1.0.SLDPRT

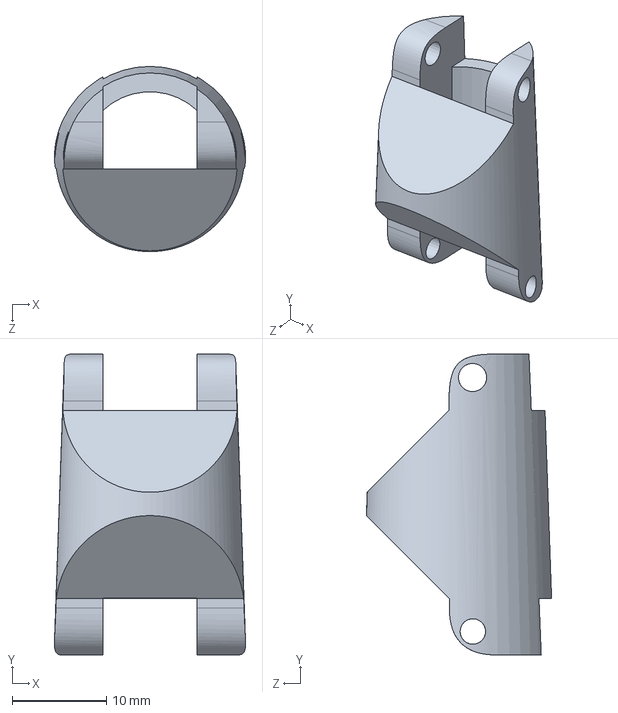
[picture p200: CAD file, 2022-01-19]
Design/Fingers/3rdDigit/1.x/MBase1.0.SLDPRT
20.3 x 32.0 x 19.7 mm
