mustafab0/Bionic-Arm/Design/Fingers/5thDigit/1.x/PCap1.0.SLDPRT

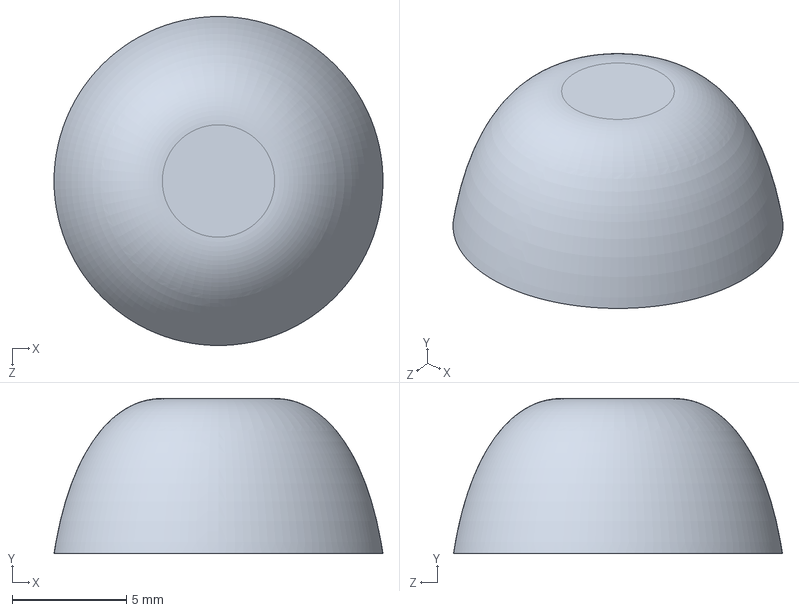
[picture p201: CAD file, 2022-01-19]
Design/Fingers/5thDigit/1.x/PCap1.0.SLDPRT
14.4 x 6.80 x 14.4 mm
