mustafab0/Bionic-Arm/Design/Fingers/5thDigit/2.x/pProximal2.0a.SLDPRT

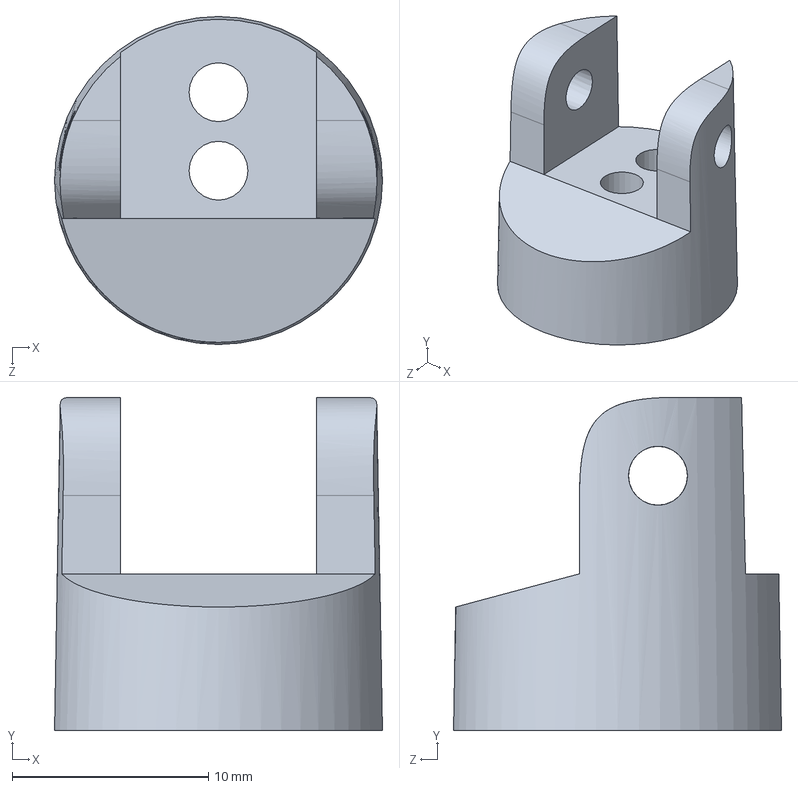
[picture p202: CAD file, 2022-01-19]
Design/Fingers/5thDigit/2.x/pProximal2.0a.SLDPRT
16.7 x 17.0 x 16.7 mm
