mustafab0/Bionic-Arm/Design/Palm/1.x/Palm1.0.SLDPRT

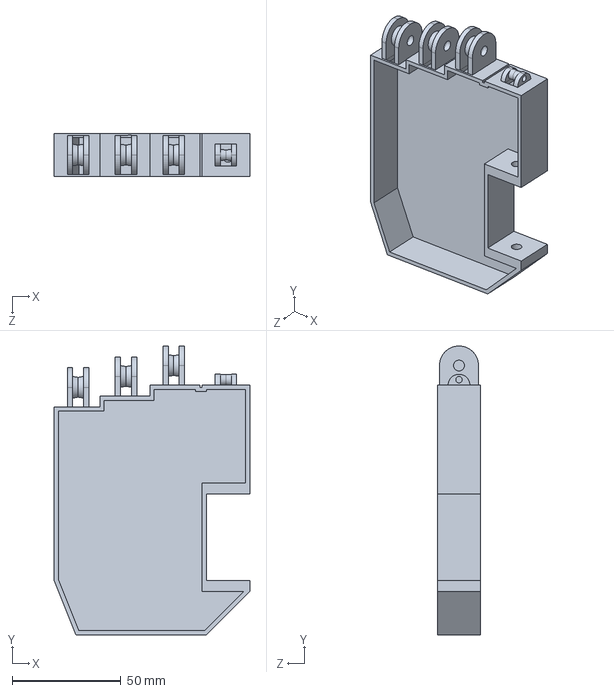
[picture p203: CAD file, 2022-01-19]
Design/Palm/1.x/Palm1.0.SLDPRT
90.0 x 133.0 x 20.0 mm
