mustafab0/Bionic-Arm/Design/Final/Shaft for coupling n.SLDPRT

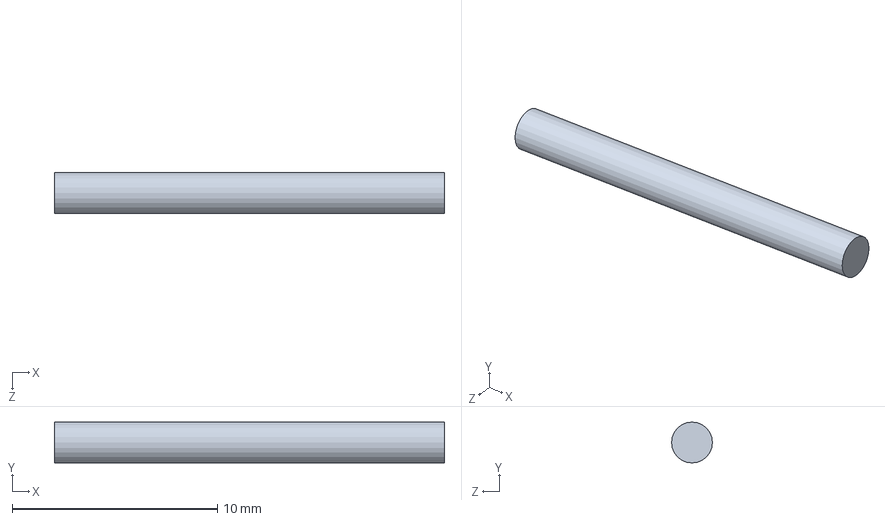
[picture p204: CAD file, 2022-01-19]
Design/Final/Shaft for coupling n.SLDPRT
19.0 x 2.00 x 2.00 mm
