mustafab0/Bionic-Arm/Design/Fingers/2ndDigit/1.x/ITop1.2.SLDPRT

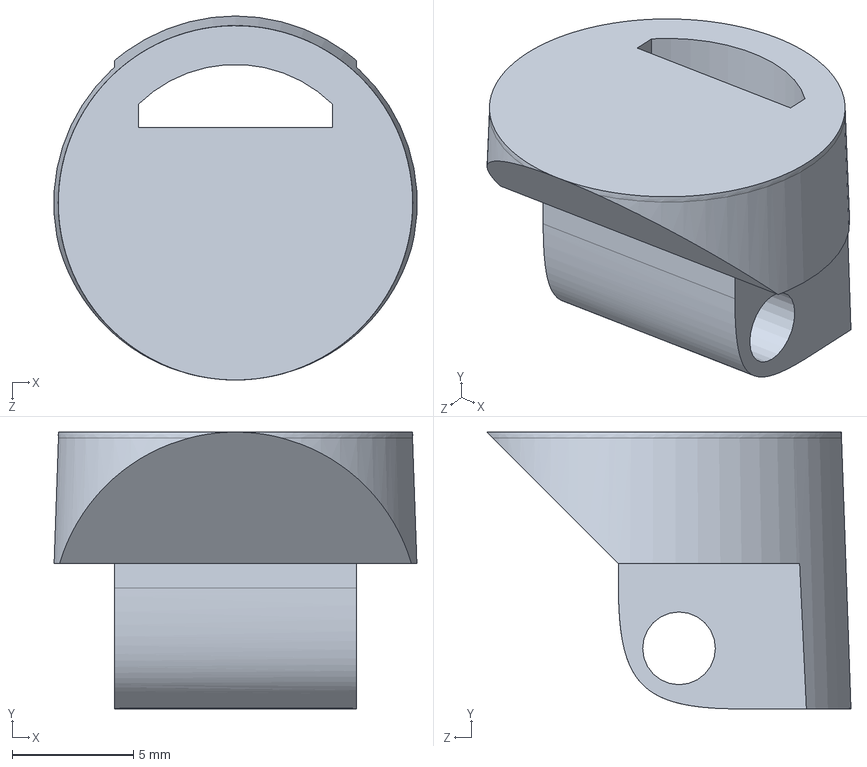
[picture p205: CAD file, 2022-01-19]
Design/Fingers/2ndDigit/1.x/ITop1.2.SLDPRT
15.0 x 11.4 x 15.0 mm
