mustafab0/Bionic-Arm/Design/Fingers/2ndDigit/2.x/2.0/UpperBase2.0.sldprt

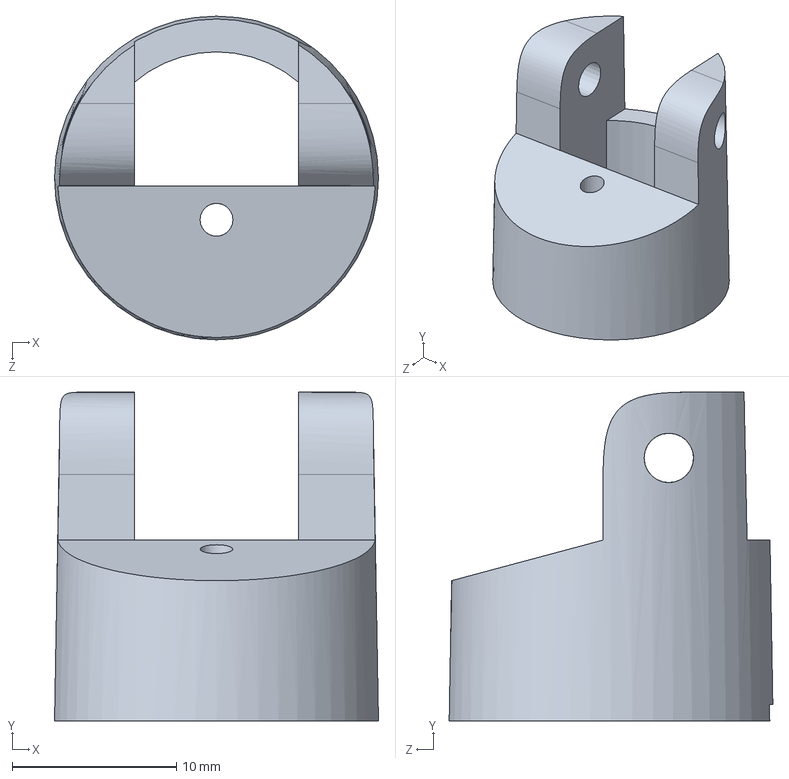
[picture p206: CAD file, 2022-01-19]
Design/Fingers/2ndDigit/2.x/2.0/UpperBase2.0.sldprt
19.7 x 20.0 x 19.7 mm
