mustafab0/Bionic-Arm/Design/Fingers/3rdDigit/1.x/MCap1.1.1.SLDPRT

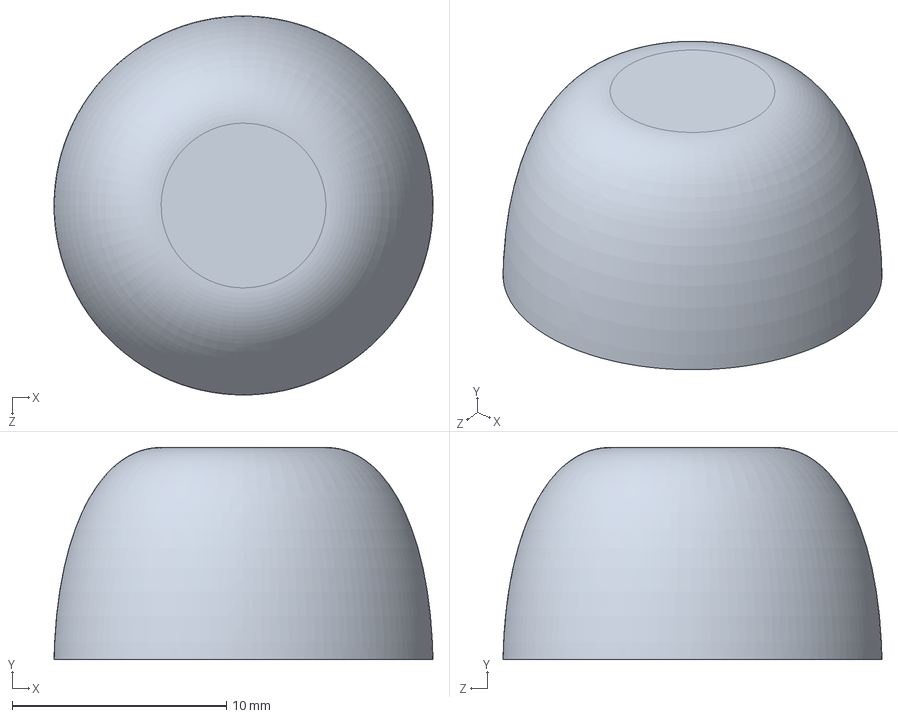
[picture p207: CAD file, 2022-01-19]
Design/Fingers/3rdDigit/1.x/MCap1.1.1.SLDPRT
17.7 x 9.90 x 17.7 mm
