mustafab0/Bionic-Arm/Design/Fingers/5thDigit/1.x/PBase1.0.SLDPRT

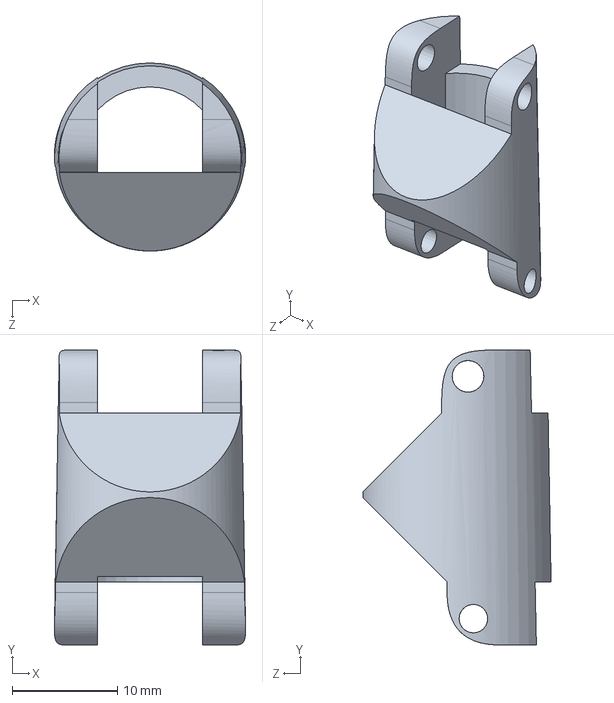
[picture p208: CAD file, 2022-01-19]
Design/Fingers/5thDigit/1.x/PBase1.0.SLDPRT
18.2 x 28.0 x 17.9 mm
