mustafab0/Bionic-Arm/Design/Fingers/5thDigit/2.x/pProximal2.0b.SLDPRT

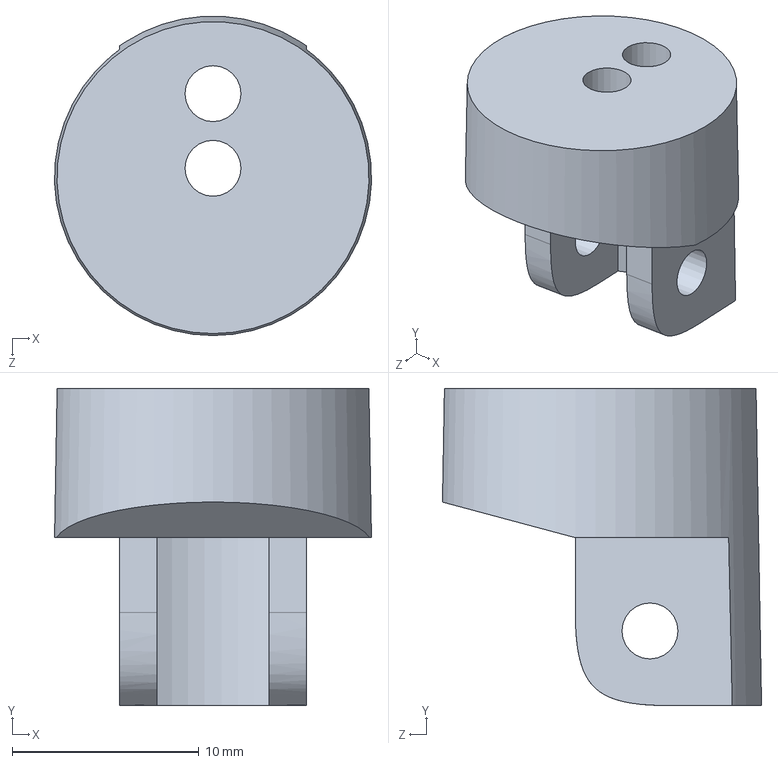
[picture p209: CAD file, 2022-01-19]
Design/Fingers/5thDigit/2.x/pProximal2.0b.SLDPRT
17.0 x 17.0 x 17.1 mm
