mustafab0/Bionic-Arm/Design/Palm/1.x/Palm1.1.SLDPRT

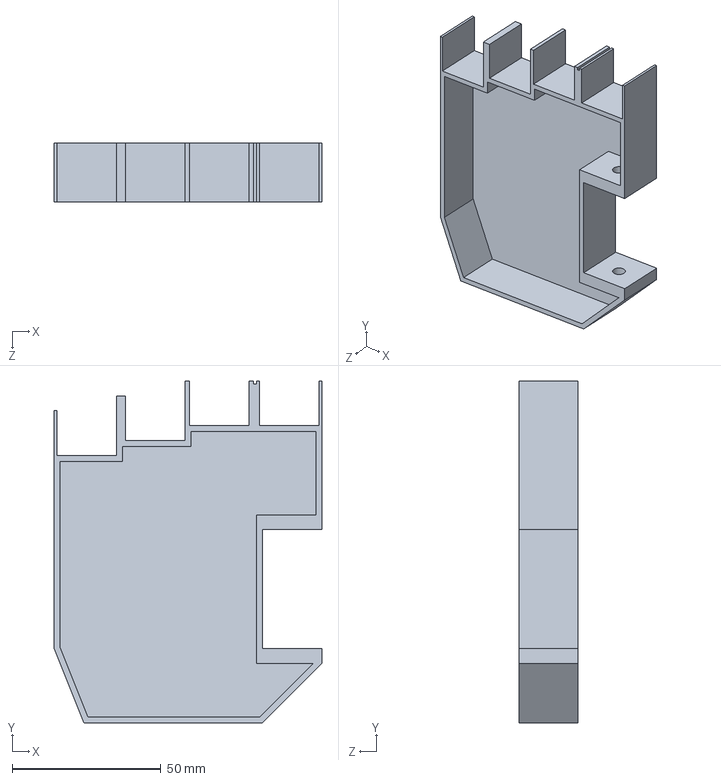
[picture p210: CAD file, 2022-01-19]
Design/Palm/1.x/Palm1.1.SLDPRT
90.0 x 115.0 x 20.0 mm
