mustafab0/Bionic-Arm/Design/Final/Coupling.SLDPRT

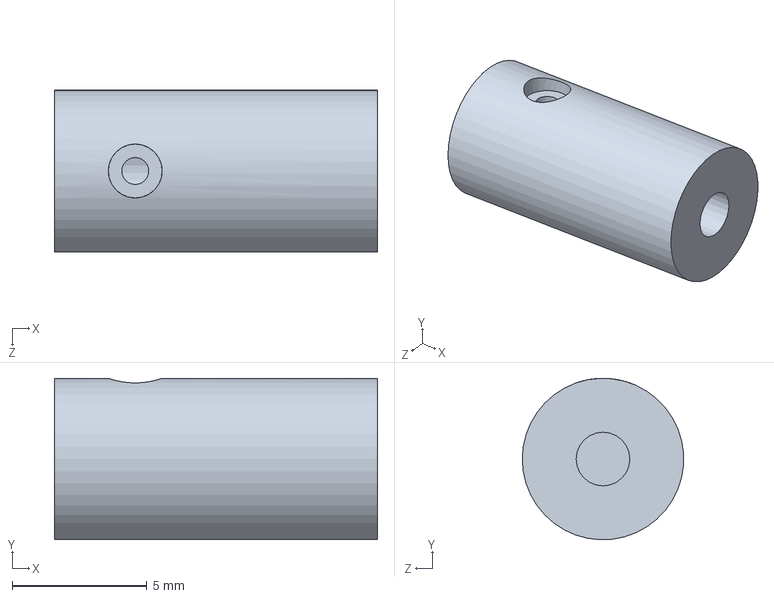
[picture p211: CAD file, 2022-01-19]
Design/Final/Coupling.SLDPRT
12.0 x 6.00 x 6.00 mm
