mustafab0/Bionic-Arm/Design/Fingers/1stDigit/1.x/TMid1.0.SLDPRT

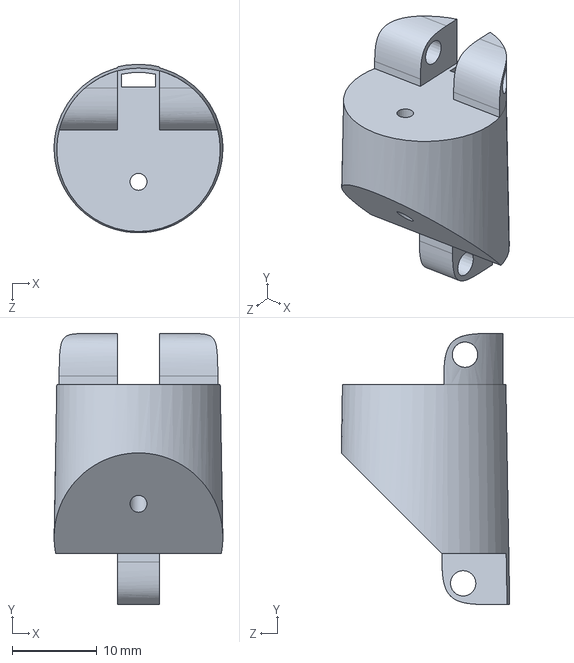
[picture p212: CAD file, 2022-01-19]
Design/Fingers/1stDigit/1.x/TMid1.0.SLDPRT
19.9 x 32.0 x 19.9 mm
