mustafab0/Bionic-Arm/Design/Fingers/2ndDigit/1.x/IBase1.1.SLDPRT

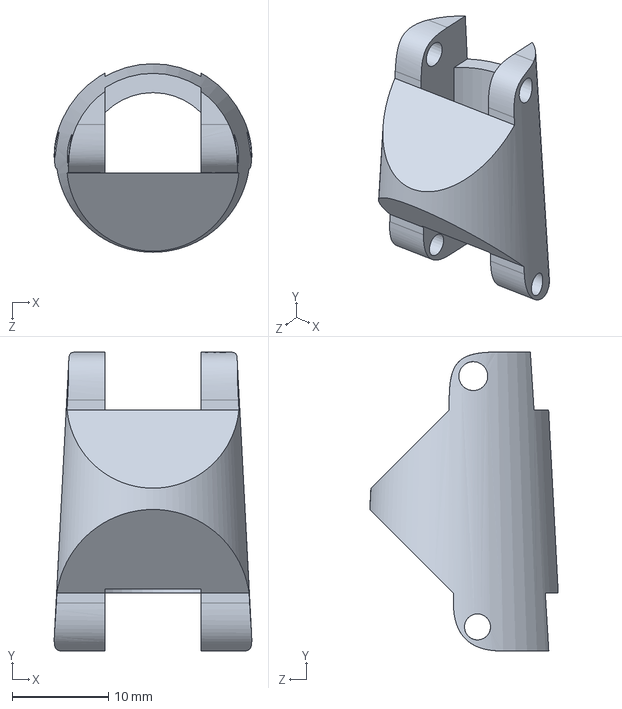
[picture p213: CAD file, 2022-01-19]
Design/Fingers/2ndDigit/1.x/IBase1.1.SLDPRT
20.5 x 31.0 x 19.5 mm
